arturlangner/Open-OBD2-datalogger/software/obdlogger/Includes/MKE06Z4.h

/*
** ###################################################################
**     Compilers:           ARM Compiler
**                          Freescale C/C++ for Embedded ARM
**                          GNU C Compiler
**                          GNU C Compiler - CodeSourcery Sourcery G++
**                          IAR ANSI C/C++ Compiler for ARM
**
**     Reference manual:    MKE06P80M48SF0RM, Rev. 1, Dec 2013
**     Version:             rev. 1.4, 2014-05-28
**     Build:               b140528
**
**     Abstract:
**         CMSIS Peripheral Access Layer for MKE06Z4
**
**     Copyright (c) 1997 - 2015 Freescale Semiconductor, Inc.
**     All rights reserved.
**
**     Redistribution and use in source and binary forms, with or without modification,
**     are permitted provided that the following conditions are met:
**
**     o Redistributions of source code must retain the above copyright notice, this list
**       of conditions and the following disclaimer.
**
**     o Redistributions in binary form must reproduce the above copyright notice, this
**       list of conditions and the following disclaimer in the documentation and/or
**       other materials provided with the distribution.
**
**     o Neither the name of Freescale Semiconductor, Inc. nor the names of its
**       contributors may be used to endorse or promote products derived from this
**       software without specific prior written permission.
**
**     THIS SOFTWARE IS PROVIDED BY THE COPYRIGHT HOLDERS AND CONTRIBUTORS "AS IS" AND
**     ANY EXPRESS OR IMPLIED WARRANTIES, INCLUDING, BUT NOT LIMITED TO, THE IMPLIED
**     WARRANTIES OF MERCHANTABILITY AND FITNESS FOR A PARTICULAR PURPOSE ARE
**     DISCLAIMED. IN NO EVENT SHALL THE COPYRIGHT HOLDER OR CONTRIBUTORS BE LIABLE FOR
**     ANY DIRECT, INDIRECT, INCIDENTAL, SPECIAL, EXEMPLARY, OR CONSEQUENTIAL DAMAGES
**     (INCLUDING, BUT NOT LIMITED TO, PROCUREMENT OF SUBSTITUTE GOODS OR SERVICES;
**     LOSS OF USE, DATA, OR PROFITS; OR BUSINESS INTERRUPTION) HOWEVER CAUSED AND ON
**     ANY THEORY OF LIABILITY, WHETHER IN CONTRACT, STRICT LIABILITY, OR TORT
**     (INCLUDING NEGLIGENCE OR OTHERWISE) ARISING IN ANY WAY OUT OF THE USE OF THIS
**     SOFTWARE, EVEN IF ADVISED OF THE POSSIBILITY OF SUCH DAMAGE.
**
**     http:                 www.freescale.com
**     mail:                 support@freescale.com
**
**     Revisions:
**     - rev. 1.0 (2013-07-30)
**         Initial version.
**     - rev. 1.1 (2013-10-29)
**         Definition of BITBAND macros updated to support peripherals with 32-bit acces disabled.
**     - rev. 1.2 (2013-10-30)
**         Update according to reference manual rev. 1.
**     - rev. 1.3 (2014-01-10)
**         CAN module: corrected address of TSIDR1 register.
**         CAN module: corrected name of MSCAN_TDLR bit DLC to TDLC.
**         FTM0 module: added access macro for EXTTRIG register.
**         NVIC module: registers access macros improved.
**         SCB module: unused bits removed, mask, shift macros improved.
**         Defines of interrupt vectors aligned to RM.
**     - rev. 1.4 (2014-05-28)
**         The declaration of clock configurations has been moved to separate header file system_MKE02Z2.h
**         Module access macro {module}_BASES replaced by {module}_BASE_PTRS.
**         I2C module: renamed status register S to S1 to match RM naming.
**
** ###################################################################
*/

/*!
 * @file MKE06Z4.h
 * @version 1.4
 * @date 2014-05-28
 * @brief CMSIS Peripheral Access Layer for MKE06Z4
 *
 * CMSIS Peripheral Access Layer for MKE06Z4
 */


/* ----------------------------------------------------------------------------
   -- MCU activation
   ---------------------------------------------------------------------------- */

/* Prevention from multiple including the same memory map */
#if !defined(MKE06Z4_H_)  /* Check if memory map has not been already included */
#define MKE06Z4_H_
#define MCU_MKE06Z4

/* Check if another memory map has not been also included */
#if (defined(MCU_ACTIVE))
  #error MKE06Z4 memory map: There is already included another memory map. Only one memory map can be included.
#endif /* (defined(MCU_ACTIVE)) */
#define MCU_ACTIVE

#include <stdint.h>

/** Memory map major version (memory maps with equal major version number are
 * compatible) */
#define MCU_MEM_MAP_VERSION 0x0100u
/** Memory map minor version */
#define MCU_MEM_MAP_VERSION_MINOR 0x0004u


/* ----------------------------------------------------------------------------
   -- Interrupt vector numbers
   ---------------------------------------------------------------------------- */

/*!
 * @addtogroup Interrupt_vector_numbers Interrupt vector numbers
 * @{
 */

/** Interrupt Number Definitions */
#define NUMBER_OF_INT_VECTORS 48                 /**< Number of interrupts in the Vector table */

typedef enum IRQn {
  /* Core interrupts */
  NonMaskableInt_IRQn          = -14,              /**< Non Maskable Interrupt */
  HardFault_IRQn               = -13,              /**< Cortex-M0 SV Hard Fault Interrupt */
  SVCall_IRQn                  = -5,               /**< Cortex-M0 SV Call Interrupt */
  PendSV_IRQn                  = -2,               /**< Cortex-M0 Pend SV Interrupt */
  SysTick_IRQn                 = -1,               /**< Cortex-M0 System Tick Interrupt */

  /* Device specific interrupts */
  Reserved16_IRQn              = 0,                /**< Reserved interrupt */
  Reserved17_IRQn              = 1,                /**< Reserved interrupt */
  Reserved18_IRQn              = 2,                /**< Reserved interrupt */
  Reserved19_IRQn              = 3,                /**< Reserved interrupt */
  Reserved20_IRQn              = 4,                /**< Reserved interrupt */
  FTMRE_IRQn                   = 5,                /**< Command complete and read collision */
  PMC_IRQn                     = 6,                /**< Low-voltage detect, low-voltage warning */
  IRQ_IRQn                     = 7,                /**< External Interrupt */
  I2C0_IRQn                    = 8,                /**< I2C0 interrupt */
  I2C1_IRQn                    = 9,                /**< I2C1 interrupt */
  SPI0_IRQn                    = 10,               /**< SPI0 single interrupt vector for all sources */
  SPI1_IRQn                    = 11,               /**< SPI1 single interrupt vector for all sources */
  UART0_IRQn                   = 12,               /**< UART0 status and error */
  UART1_IRQn                   = 13,               /**< UART1 status and error */
  UART2_IRQn                   = 14,               /**< UART2 status and error */
  ADC_IRQn                     = 15,               /**< ADC interrupt */
  ACMP0_IRQn                   = 16,               /**< ACMP0 interrupt */
  FTM0_IRQn                    = 17,               /**< FTM0 single interrupt vector for all sources */
  FTM1_IRQn                    = 18,               /**< FTM1 single interrupt vector for all sources */
  FTM2_IRQn                    = 19,               /**< FTM2 single interrupt vector for all sources */
  RTC_IRQn                     = 20,               /**< RTC overflow */
  ACMP1_IRQn                   = 21,               /**< ACMP1 interrupt */
  PIT_CH0_IRQn                 = 22,               /**< PIT CH0 overflow */
  PIT_CH1_IRQn                 = 23,               /**< PIT CH1 overflow */
  KBI0_IRQn                    = 24,               /**< Keyboard interrupt0(32bit) */
  KBI1_IRQn                    = 25,               /**< Keyboard interrupt1(32bit) */
  Reserved42_IRQn              = 26,               /**< Reserved interrupt */
  ICS_IRQn                     = 27,               /**< ICS interrupt */
  WDOG_IRQn                    = 28,               /**< Watchdog timeout */
  PWT_IRQn                     = 29,               /**< PWT interrupt */
  MSCAN_RX_IRQn                = 30,               /**< MSCAN Rx Interrupt */
  MSCAN_TX_IRQn                = 31                /**< MSCAN Tx, Err and Wake-up interrupt */
} IRQn_Type;

/*!
 * @}
 */ /* end of group Interrupt_vector_numbers */


/* ----------------------------------------------------------------------------
   -- Cortex M0 Core Configuration
   ---------------------------------------------------------------------------- */

/*!
 * @addtogroup Cortex_Core_Configuration Cortex M0 Core Configuration
 * @{
 */

#define __CM0PLUS_REV                  0x0000    /**< Core revision r0p0 */
#define __MPU_PRESENT                  0         /**< Defines if an MPU is present or not */
#define __VTOR_PRESENT                 1         /**< Defines if an MPU is present or not */
#define __NVIC_PRIO_BITS               2         /**< Number of priority bits implemented in the NVIC */
#define __Vendor_SysTickConfig         0         /**< Vendor specific implementation of SysTickConfig is defined */

#include "core_cm0plus.h"              /* Core Peripheral Access Layer */
#include "system_MKE06Z4.h"            /* Device specific configuration file */

/*!
 * @}
 */ /* end of group Cortex_Core_Configuration */


/* ----------------------------------------------------------------------------
   -- Device Peripheral Access Layer
   ---------------------------------------------------------------------------- */

/*!
 * @addtogroup Peripheral_access_layer Device Peripheral Access Layer
 * @{
 */


/*
** Start of section using anonymous unions
*/

#if defined(__ARMCC_VERSION)
  #pragma push
  #pragma anon_unions
#elif defined(__CWCC__)
  #pragma push
  #pragma cpp_extensions on
#elif defined(__GNUC__)
  /* anonymous unions are enabled by default */
#elif defined(__IAR_SYSTEMS_ICC__)
  #pragma language=extended
#else
  #error Not supported compiler type
#endif

/* ----------------------------------------------------------------------------
   -- ACMP Peripheral Access Layer
   ---------------------------------------------------------------------------- */

/*!
 * @addtogroup ACMP_Peripheral_Access_Layer ACMP Peripheral Access Layer
 * @{
 */

/** ACMP - Register Layout Typedef */
typedef struct {
  __IO uint8_t CS;                                 /**< ACMP Control and Status Register, offset: 0x0 */
  __IO uint8_t C0;                                 /**< ACMP Control Register 0, offset: 0x1 */
  __IO uint8_t C1;                                 /**< ACMP Control Register 1, offset: 0x2 */
  __IO uint8_t C2;                                 /**< ACMP Control Register 2, offset: 0x3 */
} ACMP_Type, *ACMP_MemMapPtr;

/* ----------------------------------------------------------------------------
   -- ACMP - Register accessor macros
   ---------------------------------------------------------------------------- */

/*!
 * @addtogroup ACMP_Register_Accessor_Macros ACMP - Register accessor macros
 * @{
 */


/* ACMP - Register accessors */
#define ACMP_CS_REG(base)                        ((base)->CS)
#define ACMP_C0_REG(base)                        ((base)->C0)
#define ACMP_C1_REG(base)                        ((base)->C1)
#define ACMP_C2_REG(base)                        ((base)->C2)

/*!
 * @}
 */ /* end of group ACMP_Register_Accessor_Macros */


/* ----------------------------------------------------------------------------
   -- ACMP Register Masks
   ---------------------------------------------------------------------------- */

/*!
 * @addtogroup ACMP_Register_Masks ACMP Register Masks
 * @{
 */

/* CS Bit Fields */
#define ACMP_CS_ACMOD_MASK                       0x3u
#define ACMP_CS_ACMOD_SHIFT                      0
#define ACMP_CS_ACMOD(x)                         (((uint8_t)(((uint8_t)(x))<<ACMP_CS_ACMOD_SHIFT))&ACMP_CS_ACMOD_MASK)
#define ACMP_CS_ACOPE_MASK                       0x4u
#define ACMP_CS_ACOPE_SHIFT                      2
#define ACMP_CS_ACO_MASK                         0x8u
#define ACMP_CS_ACO_SHIFT                        3
#define ACMP_CS_ACIE_MASK                        0x10u
#define ACMP_CS_ACIE_SHIFT                       4
#define ACMP_CS_ACF_MASK                         0x20u
#define ACMP_CS_ACF_SHIFT                        5
#define ACMP_CS_HYST_MASK                        0x40u
#define ACMP_CS_HYST_SHIFT                       6
#define ACMP_CS_ACE_MASK                         0x80u
#define ACMP_CS_ACE_SHIFT                        7
/* C0 Bit Fields */
#define ACMP_C0_ACNSEL_MASK                      0x3u
#define ACMP_C0_ACNSEL_SHIFT                     0
#define ACMP_C0_ACNSEL(x)                        (((uint8_t)(((uint8_t)(x))<<ACMP_C0_ACNSEL_SHIFT))&ACMP_C0_ACNSEL_MASK)
#define ACMP_C0_ACPSEL_MASK                      0x30u
#define ACMP_C0_ACPSEL_SHIFT                     4
#define ACMP_C0_ACPSEL(x)                        (((uint8_t)(((uint8_t)(x))<<ACMP_C0_ACPSEL_SHIFT))&ACMP_C0_ACPSEL_MASK)
/* C1 Bit Fields */
#define ACMP_C1_DACVAL_MASK                      0x3Fu
#define ACMP_C1_DACVAL_SHIFT                     0
#define ACMP_C1_DACVAL(x)                        (((uint8_t)(((uint8_t)(x))<<ACMP_C1_DACVAL_SHIFT))&ACMP_C1_DACVAL_MASK)
#define ACMP_C1_DACREF_MASK                      0x40u
#define ACMP_C1_DACREF_SHIFT                     6
#define ACMP_C1_DACEN_MASK                       0x80u
#define ACMP_C1_DACEN_SHIFT                      7
/* C2 Bit Fields */
#define ACMP_C2_ACIPE_MASK                       0x7u
#define ACMP_C2_ACIPE_SHIFT                      0
#define ACMP_C2_ACIPE(x)                         (((uint8_t)(((uint8_t)(x))<<ACMP_C2_ACIPE_SHIFT))&ACMP_C2_ACIPE_MASK)

/*!
 * @}
 */ /* end of group ACMP_Register_Masks */


/* ACMP - Peripheral instance base addresses */
/** Peripheral ACMP0 base address */
#define ACMP0_BASE                               (0x40073000u)
/** Peripheral ACMP0 base pointer */
#define ACMP0                                    ((ACMP_Type *)ACMP0_BASE)
#define ACMP0_BASE_PTR                           (ACMP0)
/** Peripheral ACMP1 base address */
#define ACMP1_BASE                               (0x40074000u)
/** Peripheral ACMP1 base pointer */
#define ACMP1                                    ((ACMP_Type *)ACMP1_BASE)
#define ACMP1_BASE_PTR                           (ACMP1)
/** Array initializer of ACMP peripheral base addresses */
#define ACMP_BASE_ADDRS                          { ACMP0_BASE, ACMP1_BASE }
/** Array initializer of ACMP peripheral base pointers */
#define ACMP_BASE_PTRS                           { ACMP0, ACMP1 }

/* ----------------------------------------------------------------------------
   -- ACMP - Register accessor macros
   ---------------------------------------------------------------------------- */

/*!
 * @addtogroup ACMP_Register_Accessor_Macros ACMP - Register accessor macros
 * @{
 */


/* ACMP - Register instance definitions */
/* ACMP0 */
#define ACMP0_CS                                 ACMP_CS_REG(ACMP0)
#define ACMP0_C0                                 ACMP_C0_REG(ACMP0)
#define ACMP0_C1                                 ACMP_C1_REG(ACMP0)
#define ACMP0_C2                                 ACMP_C2_REG(ACMP0)
/* ACMP1 */
#define ACMP1_CS                                 ACMP_CS_REG(ACMP1)
#define ACMP1_C0                                 ACMP_C0_REG(ACMP1)
#define ACMP1_C1                                 ACMP_C1_REG(ACMP1)
#define ACMP1_C2                                 ACMP_C2_REG(ACMP1)

/*!
 * @}
 */ /* end of group ACMP_Register_Accessor_Macros */


/*!
 * @}
 */ /* end of group ACMP_Peripheral_Access_Layer */


/* ----------------------------------------------------------------------------
   -- ADC Peripheral Access Layer
   ---------------------------------------------------------------------------- */

/*!
 * @addtogroup ADC_Peripheral_Access_Layer ADC Peripheral Access Layer
 * @{
 */

/** ADC - Register Layout Typedef */
typedef struct {
  __IO uint32_t SC1;                               /**< Status and Control Register 1, offset: 0x0 */
  __IO uint32_t SC2;                               /**< Status and Control Register 2, offset: 0x4 */
  __IO uint32_t SC3;                               /**< Status and Control Register 3, offset: 0x8 */
  __IO uint32_t SC4;                               /**< Status and Control Register 4, offset: 0xC */
  __I  uint32_t R;                                 /**< Conversion Result Register, offset: 0x10 */
  __IO uint32_t CV;                                /**< Compare Value Register, offset: 0x14 */
  __IO uint32_t APCTL1;                            /**< Pin Control 1 Register, offset: 0x18 */
  __IO uint32_t SC5;                               /**< Status and Control Register 5, offset: 0x1C */
} ADC_Type, *ADC_MemMapPtr;

/* ----------------------------------------------------------------------------
   -- ADC - Register accessor macros
   ---------------------------------------------------------------------------- */

/*!
 * @addtogroup ADC_Register_Accessor_Macros ADC - Register accessor macros
 * @{
 */


/* ADC - Register accessors */
#define ADC_SC1_REG(base)                        ((base)->SC1)
#define ADC_SC2_REG(base)                        ((base)->SC2)
#define ADC_SC3_REG(base)                        ((base)->SC3)
#define ADC_SC4_REG(base)                        ((base)->SC4)
#define ADC_R_REG(base)                          ((base)->R)
#define ADC_CV_REG(base)                         ((base)->CV)
#define ADC_APCTL1_REG(base)                     ((base)->APCTL1)
#define ADC_SC5_REG(base)                        ((base)->SC5)

/*!
 * @}
 */ /* end of group ADC_Register_Accessor_Macros */


/* ----------------------------------------------------------------------------
   -- ADC Register Masks
   ---------------------------------------------------------------------------- */

/*!
 * @addtogroup ADC_Register_Masks ADC Register Masks
 * @{
 */

/* SC1 Bit Fields */
#define ADC_SC1_ADCH_MASK                        0x1Fu
#define ADC_SC1_ADCH_SHIFT                       0
#define ADC_SC1_ADCH(x)                          (((uint32_t)(((uint32_t)(x))<<ADC_SC1_ADCH_SHIFT))&ADC_SC1_ADCH_MASK)
#define ADC_SC1_ADCO_MASK                        0x20u
#define ADC_SC1_ADCO_SHIFT                       5
#define ADC_SC1_AIEN_MASK                        0x40u
#define ADC_SC1_AIEN_SHIFT                       6
#define ADC_SC1_COCO_MASK                        0x80u
#define ADC_SC1_COCO_SHIFT                       7
/* SC2 Bit Fields */
#define ADC_SC2_REFSEL_MASK                      0x3u
#define ADC_SC2_REFSEL_SHIFT                     0
#define ADC_SC2_REFSEL(x)                        (((uint32_t)(((uint32_t)(x))<<ADC_SC2_REFSEL_SHIFT))&ADC_SC2_REFSEL_MASK)
#define ADC_SC2_FFULL_MASK                       0x4u
#define ADC_SC2_FFULL_SHIFT                      2
#define ADC_SC2_FEMPTY_MASK                      0x8u
#define ADC_SC2_FEMPTY_SHIFT                     3
#define ADC_SC2_ACFGT_MASK                       0x10u
#define ADC_SC2_ACFGT_SHIFT                      4
#define ADC_SC2_ACFE_MASK                        0x20u
#define ADC_SC2_ACFE_SHIFT                       5
#define ADC_SC2_ADTRG_MASK                       0x40u
#define ADC_SC2_ADTRG_SHIFT                      6
#define ADC_SC2_ADACT_MASK                       0x80u
#define ADC_SC2_ADACT_SHIFT                      7
/* SC3 Bit Fields */
#define ADC_SC3_ADICLK_MASK                      0x3u
#define ADC_SC3_ADICLK_SHIFT                     0
#define ADC_SC3_ADICLK(x)                        (((uint32_t)(((uint32_t)(x))<<ADC_SC3_ADICLK_SHIFT))&ADC_SC3_ADICLK_MASK)
#define ADC_SC3_MODE_MASK                        0xCu
#define ADC_SC3_MODE_SHIFT                       2
#define ADC_SC3_MODE(x)                          (((uint32_t)(((uint32_t)(x))<<ADC_SC3_MODE_SHIFT))&ADC_SC3_MODE_MASK)
#define ADC_SC3_ADLSMP_MASK                      0x10u
#define ADC_SC3_ADLSMP_SHIFT                     4
#define ADC_SC3_ADIV_MASK                        0x60u
#define ADC_SC3_ADIV_SHIFT                       5
#define ADC_SC3_ADIV(x)                          (((uint32_t)(((uint32_t)(x))<<ADC_SC3_ADIV_SHIFT))&ADC_SC3_ADIV_MASK)
#define ADC_SC3_ADLPC_MASK                       0x80u
#define ADC_SC3_ADLPC_SHIFT                      7
/* SC4 Bit Fields */
#define ADC_SC4_AFDEP_MASK                       0x7u
#define ADC_SC4_AFDEP_SHIFT                      0
#define ADC_SC4_AFDEP(x)                         (((uint32_t)(((uint32_t)(x))<<ADC_SC4_AFDEP_SHIFT))&ADC_SC4_AFDEP_MASK)
#define ADC_SC4_ACFSEL_MASK                      0x20u
#define ADC_SC4_ACFSEL_SHIFT                     5
#define ADC_SC4_ASCANE_MASK                      0x40u
#define ADC_SC4_ASCANE_SHIFT                     6
#define ADC_SC4_HTRGME_MASK                      0x100u
#define ADC_SC4_HTRGME_SHIFT                     8
/* R Bit Fields */
#define ADC_R_ADR_MASK                           0xFFFu
#define ADC_R_ADR_SHIFT                          0
#define ADC_R_ADR(x)                             (((uint32_t)(((uint32_t)(x))<<ADC_R_ADR_SHIFT))&ADC_R_ADR_MASK)
/* CV Bit Fields */
#define ADC_CV_CV_MASK                           0xFFFu
#define ADC_CV_CV_SHIFT                          0
#define ADC_CV_CV(x)                             (((uint32_t)(((uint32_t)(x))<<ADC_CV_CV_SHIFT))&ADC_CV_CV_MASK)
/* APCTL1 Bit Fields */
#define ADC_APCTL1_ADPC_MASK                     0xFFFFu
#define ADC_APCTL1_ADPC_SHIFT                    0
#define ADC_APCTL1_ADPC(x)                       (((uint32_t)(((uint32_t)(x))<<ADC_APCTL1_ADPC_SHIFT))&ADC_APCTL1_ADPC_MASK)
/* SC5 Bit Fields */
#define ADC_SC5_HTRGMASKSEL_MASK                 0x1u
#define ADC_SC5_HTRGMASKSEL_SHIFT                0
#define ADC_SC5_HTRGMASKE_MASK                   0x2u
#define ADC_SC5_HTRGMASKE_SHIFT                  1

/*!
 * @}
 */ /* end of group ADC_Register_Masks */


/* ADC - Peripheral instance base addresses */
/** Peripheral ADC base address */
#define ADC_BASE                                 (0x4003B000u)
/** Peripheral ADC base pointer */
#define ADC                                      ((ADC_Type *)ADC_BASE)
#define ADC_BASE_PTR                             (ADC)
/** Array initializer of ADC peripheral base addresses */
#define ADC_BASE_ADDRS                           { ADC_BASE }
/** Array initializer of ADC peripheral base pointers */
#define ADC_BASE_PTRS                            { ADC }

/* ----------------------------------------------------------------------------
   -- ADC - Register accessor macros
   ---------------------------------------------------------------------------- */

/*!
 * @addtogroup ADC_Register_Accessor_Macros ADC - Register accessor macros
 * @{
 */


/* ADC - Register instance definitions */
/* ADC */
#define ADC_SC1                                  ADC_SC1_REG(ADC)
#define ADC_SC2                                  ADC_SC2_REG(ADC)
#define ADC_SC3                                  ADC_SC3_REG(ADC)
#define ADC_SC4                                  ADC_SC4_REG(ADC)
#define ADC_R                                    ADC_R_REG(ADC)
#define ADC_CV                                   ADC_CV_REG(ADC)
#define ADC_APCTL1                               ADC_APCTL1_REG(ADC)
#define ADC_SC5                                  ADC_SC5_REG(ADC)

/*!
 * @}
 */ /* end of group ADC_Register_Accessor_Macros */


/*!
 * @}
 */ /* end of group ADC_Peripheral_Access_Layer */


/* ----------------------------------------------------------------------------
   -- CRC Peripheral Access Layer
   ---------------------------------------------------------------------------- */

/*!
 * @addtogroup CRC_Peripheral_Access_Layer CRC Peripheral Access Layer
 * @{
 */

/** CRC - Register Layout Typedef */
typedef struct {
  union {                                          /* offset: 0x0 */
    struct {                                         /* offset: 0x0 */
      __IO uint16_t DATAL;                             /**< CRC_DATAL register., offset: 0x0 */
      __IO uint16_t DATAH;                             /**< CRC_DATAH register., offset: 0x2 */
    } ACCESS16BIT;
    __IO uint32_t DATA;                              /**< CRC Data register, offset: 0x0 */
    struct {                                         /* offset: 0x0 */
      __IO uint8_t DATALL;                             /**< CRC_DATALL register., offset: 0x0 */
      __IO uint8_t DATALU;                             /**< CRC_DATALU register., offset: 0x1 */
      __IO uint8_t DATAHL;                             /**< CRC_DATAHL register., offset: 0x2 */
      __IO uint8_t DATAHU;                             /**< CRC_DATAHU register., offset: 0x3 */
    } ACCESS8BIT;
  };
  union {                                          /* offset: 0x4 */
    struct {                                         /* offset: 0x4 */
      __IO uint16_t GPOLYL;                            /**< CRC_GPOLYL register., offset: 0x4 */
      __IO uint16_t GPOLYH;                            /**< CRC_GPOLYH register., offset: 0x6 */
    } GPOLY_ACCESS16BIT;
    __IO uint32_t GPOLY;                             /**< CRC Polynomial register, offset: 0x4 */
    struct {                                         /* offset: 0x4 */
      __IO uint8_t GPOLYLL;                            /**< CRC_GPOLYLL register., offset: 0x4 */
      __IO uint8_t GPOLYLU;                            /**< CRC_GPOLYLU register., offset: 0x5 */
      __IO uint8_t GPOLYHL;                            /**< CRC_GPOLYHL register., offset: 0x6 */
      __IO uint8_t GPOLYHU;                            /**< CRC_GPOLYHU register., offset: 0x7 */
    } GPOLY_ACCESS8BIT;
  };
  union {                                          /* offset: 0x8 */
    __IO uint32_t CTRL;                              /**< CRC Control register, offset: 0x8 */
    struct {                                         /* offset: 0x8 */
           uint8_t RESERVED_0[3];
      __IO uint8_t CTRLHU;                             /**< CRC_CTRLHU register., offset: 0xB */
    } CTRL_ACCESS8BIT;
  };
} CRC_Type, *CRC_MemMapPtr;

/* ----------------------------------------------------------------------------
   -- CRC - Register accessor macros
   ---------------------------------------------------------------------------- */

/*!
 * @addtogroup CRC_Register_Accessor_Macros CRC - Register accessor macros
 * @{
 */


/* CRC - Register accessors */
#define CRC_DATAL_REG(base)                      ((base)->ACCESS16BIT.DATAL)
#define CRC_DATAH_REG(base)                      ((base)->ACCESS16BIT.DATAH)
#define CRC_DATA_REG(base)                       ((base)->DATA)
#define CRC_DATALL_REG(base)                     ((base)->ACCESS8BIT.DATALL)
#define CRC_DATALU_REG(base)                     ((base)->ACCESS8BIT.DATALU)
#define CRC_DATAHL_REG(base)                     ((base)->ACCESS8BIT.DATAHL)
#define CRC_DATAHU_REG(base)                     ((base)->ACCESS8BIT.DATAHU)
#define CRC_GPOLYL_REG(base)                     ((base)->GPOLY_ACCESS16BIT.GPOLYL)
#define CRC_GPOLYH_REG(base)                     ((base)->GPOLY_ACCESS16BIT.GPOLYH)
#define CRC_GPOLY_REG(base)                      ((base)->GPOLY)
#define CRC_GPOLYLL_REG(base)                    ((base)->GPOLY_ACCESS8BIT.GPOLYLL)
#define CRC_GPOLYLU_REG(base)                    ((base)->GPOLY_ACCESS8BIT.GPOLYLU)
#define CRC_GPOLYHL_REG(base)                    ((base)->GPOLY_ACCESS8BIT.GPOLYHL)
#define CRC_GPOLYHU_REG(base)                    ((base)->GPOLY_ACCESS8BIT.GPOLYHU)
#define CRC_CTRL_REG(base)                       ((base)->CTRL)
#define CRC_CTRLHU_REG(base)                     ((base)->CTRL_ACCESS8BIT.CTRLHU)

/*!
 * @}
 */ /* end of group CRC_Register_Accessor_Macros */


/* ----------------------------------------------------------------------------
   -- CRC Register Masks
   ---------------------------------------------------------------------------- */

/*!
 * @addtogroup CRC_Register_Masks CRC Register Masks
 * @{
 */

/* DATAL Bit Fields */
#define CRC_DATAL_DATAL_MASK                     0xFFFFu
#define CRC_DATAL_DATAL_SHIFT                    0
#define CRC_DATAL_DATAL(x)                       (((uint16_t)(((uint16_t)(x))<<CRC_DATAL_DATAL_SHIFT))&CRC_DATAL_DATAL_MASK)
/* DATAH Bit Fields */
#define CRC_DATAH_DATAH_MASK                     0xFFFFu
#define CRC_DATAH_DATAH_SHIFT                    0
#define CRC_DATAH_DATAH(x)                       (((uint16_t)(((uint16_t)(x))<<CRC_DATAH_DATAH_SHIFT))&CRC_DATAH_DATAH_MASK)
/* DATA Bit Fields */
#define CRC_DATA_LL_MASK                         0xFFu
#define CRC_DATA_LL_SHIFT                        0
#define CRC_DATA_LL(x)                           (((uint32_t)(((uint32_t)(x))<<CRC_DATA_LL_SHIFT))&CRC_DATA_LL_MASK)
#define CRC_DATA_LU_MASK                         0xFF00u
#define CRC_DATA_LU_SHIFT                        8
#define CRC_DATA_LU(x)                           (((uint32_t)(((uint32_t)(x))<<CRC_DATA_LU_SHIFT))&CRC_DATA_LU_MASK)
#define CRC_DATA_HL_MASK                         0xFF0000u
#define CRC_DATA_HL_SHIFT                        16
#define CRC_DATA_HL(x)                           (((uint32_t)(((uint32_t)(x))<<CRC_DATA_HL_SHIFT))&CRC_DATA_HL_MASK)
#define CRC_DATA_HU_MASK                         0xFF000000u
#define CRC_DATA_HU_SHIFT                        24
#define CRC_DATA_HU(x)                           (((uint32_t)(((uint32_t)(x))<<CRC_DATA_HU_SHIFT))&CRC_DATA_HU_MASK)
/* DATALL Bit Fields */
#define CRC_DATALL_DATALL_MASK                   0xFFu
#define CRC_DATALL_DATALL_SHIFT                  0
#define CRC_DATALL_DATALL(x)                     (((uint8_t)(((uint8_t)(x))<<CRC_DATALL_DATALL_SHIFT))&CRC_DATALL_DATALL_MASK)
/* DATALU Bit Fields */
#define CRC_DATALU_DATALU_MASK                   0xFFu
#define CRC_DATALU_DATALU_SHIFT                  0
#define CRC_DATALU_DATALU(x)                     (((uint8_t)(((uint8_t)(x))<<CRC_DATALU_DATALU_SHIFT))&CRC_DATALU_DATALU_MASK)
/* DATAHL Bit Fields */
#define CRC_DATAHL_DATAHL_MASK                   0xFFu
#define CRC_DATAHL_DATAHL_SHIFT                  0
#define CRC_DATAHL_DATAHL(x)                     (((uint8_t)(((uint8_t)(x))<<CRC_DATAHL_DATAHL_SHIFT))&CRC_DATAHL_DATAHL_MASK)
/* DATAHU Bit Fields */
#define CRC_DATAHU_DATAHU_MASK                   0xFFu
#define CRC_DATAHU_DATAHU_SHIFT                  0
#define CRC_DATAHU_DATAHU(x)                     (((uint8_t)(((uint8_t)(x))<<CRC_DATAHU_DATAHU_SHIFT))&CRC_DATAHU_DATAHU_MASK)
/* GPOLYL Bit Fields */
#define CRC_GPOLYL_GPOLYL_MASK                   0xFFFFu
#define CRC_GPOLYL_GPOLYL_SHIFT                  0
#define CRC_GPOLYL_GPOLYL(x)                     (((uint16_t)(((uint16_t)(x))<<CRC_GPOLYL_GPOLYL_SHIFT))&CRC_GPOLYL_GPOLYL_MASK)
/* GPOLYH Bit Fields */
#define CRC_GPOLYH_GPOLYH_MASK                   0xFFFFu
#define CRC_GPOLYH_GPOLYH_SHIFT                  0
#define CRC_GPOLYH_GPOLYH(x)                     (((uint16_t)(((uint16_t)(x))<<CRC_GPOLYH_GPOLYH_SHIFT))&CRC_GPOLYH_GPOLYH_MASK)
/* GPOLY Bit Fields */
#define CRC_GPOLY_LOW_MASK                       0xFFFFu
#define CRC_GPOLY_LOW_SHIFT                      0
#define CRC_GPOLY_LOW(x)                         (((uint32_t)(((uint32_t)(x))<<CRC_GPOLY_LOW_SHIFT))&CRC_GPOLY_LOW_MASK)
#define CRC_GPOLY_HIGH_MASK                      0xFFFF0000u
#define CRC_GPOLY_HIGH_SHIFT                     16
#define CRC_GPOLY_HIGH(x)                        (((uint32_t)(((uint32_t)(x))<<CRC_GPOLY_HIGH_SHIFT))&CRC_GPOLY_HIGH_MASK)
/* GPOLYLL Bit Fields */
#define CRC_GPOLYLL_GPOLYLL_MASK                 0xFFu
#define CRC_GPOLYLL_GPOLYLL_SHIFT                0
#define CRC_GPOLYLL_GPOLYLL(x)                   (((uint8_t)(((uint8_t)(x))<<CRC_GPOLYLL_GPOLYLL_SHIFT))&CRC_GPOLYLL_GPOLYLL_MASK)
/* GPOLYLU Bit Fields */
#define CRC_GPOLYLU_GPOLYLU_MASK                 0xFFu
#define CRC_GPOLYLU_GPOLYLU_SHIFT                0
#define CRC_GPOLYLU_GPOLYLU(x)                   (((uint8_t)(((uint8_t)(x))<<CRC_GPOLYLU_GPOLYLU_SHIFT))&CRC_GPOLYLU_GPOLYLU_MASK)
/* GPOLYHL Bit Fields */
#define CRC_GPOLYHL_GPOLYHL_MASK                 0xFFu
#define CRC_GPOLYHL_GPOLYHL_SHIFT                0
#define CRC_GPOLYHL_GPOLYHL(x)                   (((uint8_t)(((uint8_t)(x))<<CRC_GPOLYHL_GPOLYHL_SHIFT))&CRC_GPOLYHL_GPOLYHL_MASK)
/* GPOLYHU Bit Fields */
#define CRC_GPOLYHU_GPOLYHU_MASK                 0xFFu
#define CRC_GPOLYHU_GPOLYHU_SHIFT                0
#define CRC_GPOLYHU_GPOLYHU(x)                   (((uint8_t)(((uint8_t)(x))<<CRC_GPOLYHU_GPOLYHU_SHIFT))&CRC_GPOLYHU_GPOLYHU_MASK)
/* CTRL Bit Fields */
#define CRC_CTRL_TCRC_MASK                       0x1000000u
#define CRC_CTRL_TCRC_SHIFT                      24
#define CRC_CTRL_WAS_MASK                        0x2000000u
#define CRC_CTRL_WAS_SHIFT                       25
#define CRC_CTRL_FXOR_MASK                       0x4000000u
#define CRC_CTRL_FXOR_SHIFT                      26
#define CRC_CTRL_TOTR_MASK                       0x30000000u
#define CRC_CTRL_TOTR_SHIFT                      28
#define CRC_CTRL_TOTR(x)                         (((uint32_t)(((uint32_t)(x))<<CRC_CTRL_TOTR_SHIFT))&CRC_CTRL_TOTR_MASK)
#define CRC_CTRL_TOT_MASK                        0xC0000000u
#define CRC_CTRL_TOT_SHIFT                       30
#define CRC_CTRL_TOT(x)                          (((uint32_t)(((uint32_t)(x))<<CRC_CTRL_TOT_SHIFT))&CRC_CTRL_TOT_MASK)
/* CTRLHU Bit Fields */
#define CRC_CTRLHU_TCRC_MASK                     0x1u
#define CRC_CTRLHU_TCRC_SHIFT                    0
#define CRC_CTRLHU_WAS_MASK                      0x2u
#define CRC_CTRLHU_WAS_SHIFT                     1
#define CRC_CTRLHU_FXOR_MASK                     0x4u
#define CRC_CTRLHU_FXOR_SHIFT                    2
#define CRC_CTRLHU_TOTR_MASK                     0x30u
#define CRC_CTRLHU_TOTR_SHIFT                    4
#define CRC_CTRLHU_TOTR(x)                       (((uint8_t)(((uint8_t)(x))<<CRC_CTRLHU_TOTR_SHIFT))&CRC_CTRLHU_TOTR_MASK)
#define CRC_CTRLHU_TOT_MASK                      0xC0u
#define CRC_CTRLHU_TOT_SHIFT                     6
#define CRC_CTRLHU_TOT(x)                        (((uint8_t)(((uint8_t)(x))<<CRC_CTRLHU_TOT_SHIFT))&CRC_CTRLHU_TOT_MASK)

/*!
 * @}
 */ /* end of group CRC_Register_Masks */


/* CRC - Peripheral instance base addresses */
/** Peripheral CRC base address */
#define CRC_BASE                                 (0x40032000u)
/** Peripheral CRC base pointer */
#define CRC0                                     ((CRC_Type *)CRC_BASE)
#define CRC_BASE_PTR                             (CRC0)
/** Array initializer of CRC peripheral base addresses */
#define CRC_BASE_ADDRS                           { CRC_BASE }
/** Array initializer of CRC peripheral base pointers */
#define CRC_BASE_PTRS                            { CRC0 }

/* ----------------------------------------------------------------------------
   -- CRC - Register accessor macros
   ---------------------------------------------------------------------------- */

/*!
 * @addtogroup CRC_Register_Accessor_Macros CRC - Register accessor macros
 * @{
 */


/* CRC - Register instance definitions */
/* CRC */
#define CRC_DATA                                 CRC_DATA_REG(CRC0)
#define CRC_DATAL                                CRC_DATAL_REG(CRC0)
#define CRC_DATALL                               CRC_DATALL_REG(CRC0)
#define CRC_DATALU                               CRC_DATALU_REG(CRC0)
#define CRC_DATAH                                CRC_DATAH_REG(CRC0)
#define CRC_DATAHL                               CRC_DATAHL_REG(CRC0)
#define CRC_DATAHU                               CRC_DATAHU_REG(CRC0)
#define CRC_GPOLY                                CRC_GPOLY_REG(CRC0)
#define CRC_GPOLYL                               CRC_GPOLYL_REG(CRC0)
#define CRC_GPOLYLL                              CRC_GPOLYLL_REG(CRC0)
#define CRC_GPOLYLU                              CRC_GPOLYLU_REG(CRC0)
#define CRC_GPOLYH                               CRC_GPOLYH_REG(CRC0)
#define CRC_GPOLYHL                              CRC_GPOLYHL_REG(CRC0)
#define CRC_GPOLYHU                              CRC_GPOLYHU_REG(CRC0)
#define CRC_CTRL                                 CRC_CTRL_REG(CRC0)
#define CRC_CTRLHU                               CRC_CTRLHU_REG(CRC0)

/*!
 * @}
 */ /* end of group CRC_Register_Accessor_Macros */


/*!
 * @}
 */ /* end of group CRC_Peripheral_Access_Layer */


/* ----------------------------------------------------------------------------
   -- FGPIO Peripheral Access Layer
   ---------------------------------------------------------------------------- */

/*!
 * @addtogroup FGPIO_Peripheral_Access_Layer FGPIO Peripheral Access Layer
 * @{
 */

/** FGPIO - Register Layout Typedef */
typedef struct {
  __IO uint32_t PDOR;                              /**< Port Data Output Register, offset: 0x0 */
  __O  uint32_t PSOR;                              /**< Port Set Output Register, offset: 0x4 */
  __O  uint32_t PCOR;                              /**< Port Clear Output Register, offset: 0x8 */
  __O  uint32_t PTOR;                              /**< Port Toggle Output Register, offset: 0xC */
  __I  uint32_t PDIR;                              /**< Port Data Input Register, offset: 0x10 */
  __IO uint32_t PDDR;                              /**< Port Data Direction Register, offset: 0x14 */
  __IO uint32_t PIDR;                              /**< Port Input Disable Register, offset: 0x18 */
} FGPIO_Type, *FGPIO_MemMapPtr;

/* ----------------------------------------------------------------------------
   -- FGPIO - Register accessor macros
   ---------------------------------------------------------------------------- */

/*!
 * @addtogroup FGPIO_Register_Accessor_Macros FGPIO - Register accessor macros
 * @{
 */


/* FGPIO - Register accessors */
#define FGPIO_PDOR_REG(base)                     ((base)->PDOR)
#define FGPIO_PSOR_REG(base)                     ((base)->PSOR)
#define FGPIO_PCOR_REG(base)                     ((base)->PCOR)
#define FGPIO_PTOR_REG(base)                     ((base)->PTOR)
#define FGPIO_PDIR_REG(base)                     ((base)->PDIR)
#define FGPIO_PDDR_REG(base)                     ((base)->PDDR)
#define FGPIO_PIDR_REG(base)                     ((base)->PIDR)

/*!
 * @}
 */ /* end of group FGPIO_Register_Accessor_Macros */


/* ----------------------------------------------------------------------------
   -- FGPIO Register Masks
   ---------------------------------------------------------------------------- */

/*!
 * @addtogroup FGPIO_Register_Masks FGPIO Register Masks
 * @{
 */

/* PDOR Bit Fields */
#define FGPIO_PDOR_PDO_MASK                      0xFFFFFFFFu
#define FGPIO_PDOR_PDO_SHIFT                     0
#define FGPIO_PDOR_PDO(x)                        (((uint32_t)(((uint32_t)(x))<<FGPIO_PDOR_PDO_SHIFT))&FGPIO_PDOR_PDO_MASK)
/* PSOR Bit Fields */
#define FGPIO_PSOR_PTSO_MASK                     0xFFFFFFFFu
#define FGPIO_PSOR_PTSO_SHIFT                    0
#define FGPIO_PSOR_PTSO(x)                       (((uint32_t)(((uint32_t)(x))<<FGPIO_PSOR_PTSO_SHIFT))&FGPIO_PSOR_PTSO_MASK)
/* PCOR Bit Fields */
#define FGPIO_PCOR_PTCO_MASK                     0xFFFFFFFFu
#define FGPIO_PCOR_PTCO_SHIFT                    0
#define FGPIO_PCOR_PTCO(x)                       (((uint32_t)(((uint32_t)(x))<<FGPIO_PCOR_PTCO_SHIFT))&FGPIO_PCOR_PTCO_MASK)
/* PTOR Bit Fields */
#define FGPIO_PTOR_PTTO_MASK                     0xFFFFFFFFu
#define FGPIO_PTOR_PTTO_SHIFT                    0
#define FGPIO_PTOR_PTTO(x)                       (((uint32_t)(((uint32_t)(x))<<FGPIO_PTOR_PTTO_SHIFT))&FGPIO_PTOR_PTTO_MASK)
/* PDIR Bit Fields */
#define FGPIO_PDIR_PDI_MASK                      0xFFFFFFFFu
#define FGPIO_PDIR_PDI_SHIFT                     0
#define FGPIO_PDIR_PDI(x)                        (((uint32_t)(((uint32_t)(x))<<FGPIO_PDIR_PDI_SHIFT))&FGPIO_PDIR_PDI_MASK)
/* PDDR Bit Fields */
#define FGPIO_PDDR_PDD_MASK                      0xFFFFFFFFu
#define FGPIO_PDDR_PDD_SHIFT                     0
#define FGPIO_PDDR_PDD(x)                        (((uint32_t)(((uint32_t)(x))<<FGPIO_PDDR_PDD_SHIFT))&FGPIO_PDDR_PDD_MASK)
/* PIDR Bit Fields */
#define FGPIO_PIDR_PID_MASK                      0xFFFFFFFFu
#define FGPIO_PIDR_PID_SHIFT                     0
#define FGPIO_PIDR_PID(x)                        (((uint32_t)(((uint32_t)(x))<<FGPIO_PIDR_PID_SHIFT))&FGPIO_PIDR_PID_MASK)

/*!
 * @}
 */ /* end of group FGPIO_Register_Masks */


/* FGPIO - Peripheral instance base addresses */
/** Peripheral FGPIOA base address */
#define FGPIOA_BASE                              (0xF8000000u)
/** Peripheral FGPIOA base pointer */
#define FGPIOA                                   ((FGPIO_Type *)FGPIOA_BASE)
#define FGPIOA_BASE_PTR                          (FGPIOA)
/** Peripheral FGPIOB base address */
#define FGPIOB_BASE                              (0xF8000040u)
/** Peripheral FGPIOB base pointer */
#define FGPIOB                                   ((FGPIO_Type *)FGPIOB_BASE)
#define FGPIOB_BASE_PTR                          (FGPIOB)
/** Peripheral FGPIOC base address */
#define FGPIOC_BASE                              (0xF8000080u)
/** Peripheral FGPIOC base pointer */
#define FGPIOC                                   ((FGPIO_Type *)FGPIOC_BASE)
#define FGPIOC_BASE_PTR                          (FGPIOC)
/** Array initializer of FGPIO peripheral base addresses */
#define FGPIO_BASE_ADDRS                         { FGPIOA_BASE, FGPIOB_BASE, FGPIOC_BASE }
/** Array initializer of FGPIO peripheral base pointers */
#define FGPIO_BASE_PTRS                          { FGPIOA, FGPIOB, FGPIOC }

/* ----------------------------------------------------------------------------
   -- FGPIO - Register accessor macros
   ---------------------------------------------------------------------------- */

/*!
 * @addtogroup FGPIO_Register_Accessor_Macros FGPIO - Register accessor macros
 * @{
 */


/* FGPIO - Register instance definitions */
/* FGPIOA */
#define FGPIOA_PDOR                              FGPIO_PDOR_REG(FGPIOA)
#define FGPIOA_PSOR                              FGPIO_PSOR_REG(FGPIOA)
#define FGPIOA_PCOR                              FGPIO_PCOR_REG(FGPIOA)
#define FGPIOA_PTOR                              FGPIO_PTOR_REG(FGPIOA)
#define FGPIOA_PDIR                              FGPIO_PDIR_REG(FGPIOA)
#define FGPIOA_PDDR                              FGPIO_PDDR_REG(FGPIOA)
#define FGPIOA_PIDR                              FGPIO_PIDR_REG(FGPIOA)
/* FGPIOB */
#define FGPIOB_PDOR                              FGPIO_PDOR_REG(FGPIOB)
#define FGPIOB_PSOR                              FGPIO_PSOR_REG(FGPIOB)
#define FGPIOB_PCOR                              FGPIO_PCOR_REG(FGPIOB)
#define FGPIOB_PTOR                              FGPIO_PTOR_REG(FGPIOB)
#define FGPIOB_PDIR                              FGPIO_PDIR_REG(FGPIOB)
#define FGPIOB_PDDR                              FGPIO_PDDR_REG(FGPIOB)
#define FGPIOB_PIDR                              FGPIO_PIDR_REG(FGPIOB)
/* FGPIOC */
#define FGPIOC_PDOR                              FGPIO_PDOR_REG(FGPIOC)
#define FGPIOC_PSOR                              FGPIO_PSOR_REG(FGPIOC)
#define FGPIOC_PCOR                              FGPIO_PCOR_REG(FGPIOC)
#define FGPIOC_PTOR                              FGPIO_PTOR_REG(FGPIOC)
#define FGPIOC_PDIR                              FGPIO_PDIR_REG(FGPIOC)
#define FGPIOC_PDDR                              FGPIO_PDDR_REG(FGPIOC)
#define FGPIOC_PIDR                              FGPIO_PIDR_REG(FGPIOC)

/*!
 * @}
 */ /* end of group FGPIO_Register_Accessor_Macros */


/*!
 * @}
 */ /* end of group FGPIO_Peripheral_Access_Layer */


/* ----------------------------------------------------------------------------
   -- FTM Peripheral Access Layer
   ---------------------------------------------------------------------------- */

/*!
 * @addtogroup FTM_Peripheral_Access_Layer FTM Peripheral Access Layer
 * @{
 */

/** FTM - Register Layout Typedef */
typedef struct {
  __IO uint32_t SC;                                /**< Status And Control, offset: 0x0 */
  __IO uint32_t CNT;                               /**< Counter, offset: 0x4 */
  __IO uint32_t MOD;                               /**< Modulo, offset: 0x8 */
  struct {                                         /* offset: 0xC, array step: 0x8 */
    __IO uint32_t CnSC;                              /**< Channel (n) Status And Control, array offset: 0xC, array step: 0x8 */
    __IO uint32_t CnV;                               /**< Channel (n) Value, array offset: 0x10, array step: 0x8 */
  } CONTROLS[6];
       uint8_t RESERVED_0[16];
  __IO uint32_t CNTIN;                             /**< Counter Initial Value, offset: 0x4C */
  __IO uint32_t STATUS;                            /**< Capture And Compare Status, offset: 0x50 */
  __IO uint32_t MODE;                              /**< Features Mode Selection, offset: 0x54 */
  __IO uint32_t SYNC;                              /**< Synchronization, offset: 0x58 */
  __IO uint32_t OUTINIT;                           /**< Initial State For Channels Output, offset: 0x5C */
  __IO uint32_t OUTMASK;                           /**< Output Mask, offset: 0x60 */
  __IO uint32_t COMBINE;                           /**< Function For Linked Channels, offset: 0x64 */
  __IO uint32_t DEADTIME;                          /**< Deadtime Insertion Control, offset: 0x68 */
  __IO uint32_t EXTTRIG;                           /**< FTM External Trigger, offset: 0x6C */
  __IO uint32_t POL;                               /**< Channels Polarity, offset: 0x70 */
  __IO uint32_t FMS;                               /**< Fault Mode Status, offset: 0x74 */
  __IO uint32_t FILTER;                            /**< Input Capture Filter Control, offset: 0x78 */
  __IO uint32_t FLTCTRL;                           /**< Fault Control, offset: 0x7C */
       uint8_t RESERVED_1[4];
  __IO uint32_t CONF;                              /**< Configuration, offset: 0x84 */
  __IO uint32_t FLTPOL;                            /**< FTM Fault Input Polarity, offset: 0x88 */
  __IO uint32_t SYNCONF;                           /**< Synchronization Configuration, offset: 0x8C */
  __IO uint32_t INVCTRL;                           /**< FTM Inverting Control, offset: 0x90 */
  __IO uint32_t SWOCTRL;                           /**< FTM Software Output Control, offset: 0x94 */
  __IO uint32_t PWMLOAD;                           /**< FTM PWM Load, offset: 0x98 */
} FTM_Type, *FTM_MemMapPtr;

/* ----------------------------------------------------------------------------
   -- FTM - Register accessor macros
   ---------------------------------------------------------------------------- */

/*!
 * @addtogroup FTM_Register_Accessor_Macros FTM - Register accessor macros
 * @{
 */


/* FTM - Register accessors */
#define FTM_SC_REG(base)                         ((base)->SC)
#define FTM_CNT_REG(base)                        ((base)->CNT)
#define FTM_MOD_REG(base)                        ((base)->MOD)
#define FTM_CnSC_REG(base,index)                 ((base)->CONTROLS[index].CnSC)
#define FTM_CnV_REG(base,index)                  ((base)->CONTROLS[index].CnV)
#define FTM_CNTIN_REG(base)                      ((base)->CNTIN)
#define FTM_STATUS_REG(base)                     ((base)->STATUS)
#define FTM_MODE_REG(base)                       ((base)->MODE)
#define FTM_SYNC_REG(base)                       ((base)->SYNC)
#define FTM_OUTINIT_REG(base)                    ((base)->OUTINIT)
#define FTM_OUTMASK_REG(base)                    ((base)->OUTMASK)
#define FTM_COMBINE_REG(base)                    ((base)->COMBINE)
#define FTM_DEADTIME_REG(base)                   ((base)->DEADTIME)
#define FTM_EXTTRIG_REG(base)                    ((base)->EXTTRIG)
#define FTM_POL_REG(base)                        ((base)->POL)
#define FTM_FMS_REG(base)                        ((base)->FMS)
#define FTM_FILTER_REG(base)                     ((base)->FILTER)
#define FTM_FLTCTRL_REG(base)                    ((base)->FLTCTRL)
#define FTM_CONF_REG(base)                       ((base)->CONF)
#define FTM_FLTPOL_REG(base)                     ((base)->FLTPOL)
#define FTM_SYNCONF_REG(base)                    ((base)->SYNCONF)
#define FTM_INVCTRL_REG(base)                    ((base)->INVCTRL)
#define FTM_SWOCTRL_REG(base)                    ((base)->SWOCTRL)
#define FTM_PWMLOAD_REG(base)                    ((base)->PWMLOAD)

/*!
 * @}
 */ /* end of group FTM_Register_Accessor_Macros */


/* ----------------------------------------------------------------------------
   -- FTM Register Masks
   ---------------------------------------------------------------------------- */

/*!
 * @addtogroup FTM_Register_Masks FTM Register Masks
 * @{
 */

/* SC Bit Fields */
#define FTM_SC_PS_MASK                           0x7u
#define FTM_SC_PS_SHIFT                          0
#define FTM_SC_PS(x)                             (((uint32_t)(((uint32_t)(x))<<FTM_SC_PS_SHIFT))&FTM_SC_PS_MASK)
#define FTM_SC_CLKS_MASK                         0x18u
#define FTM_SC_CLKS_SHIFT                        3
#define FTM_SC_CLKS(x)                           (((uint32_t)(((uint32_t)(x))<<FTM_SC_CLKS_SHIFT))&FTM_SC_CLKS_MASK)
#define FTM_SC_CPWMS_MASK                        0x20u
#define FTM_SC_CPWMS_SHIFT                       5
#define FTM_SC_TOIE_MASK                         0x40u
#define FTM_SC_TOIE_SHIFT                        6
#define FTM_SC_TOF_MASK                          0x80u
#define FTM_SC_TOF_SHIFT                         7
/* CNT Bit Fields */
#define FTM_CNT_COUNT_MASK                       0xFFFFu
#define FTM_CNT_COUNT_SHIFT                      0
#define FTM_CNT_COUNT(x)                         (((uint32_t)(((uint32_t)(x))<<FTM_CNT_COUNT_SHIFT))&FTM_CNT_COUNT_MASK)
/* MOD Bit Fields */
#define FTM_MOD_MOD_MASK                         0xFFFFu
#define FTM_MOD_MOD_SHIFT                        0
#define FTM_MOD_MOD(x)                           (((uint32_t)(((uint32_t)(x))<<FTM_MOD_MOD_SHIFT))&FTM_MOD_MOD_MASK)
/* CnSC Bit Fields */
#define FTM_CnSC_ELSA_MASK                       0x4u
#define FTM_CnSC_ELSA_SHIFT                      2
#define FTM_CnSC_ELSB_MASK                       0x8u
#define FTM_CnSC_ELSB_SHIFT                      3
#define FTM_CnSC_MSA_MASK                        0x10u
#define FTM_CnSC_MSA_SHIFT                       4
#define FTM_CnSC_MSB_MASK                        0x20u
#define FTM_CnSC_MSB_SHIFT                       5
#define FTM_CnSC_CHIE_MASK                       0x40u
#define FTM_CnSC_CHIE_SHIFT                      6
#define FTM_CnSC_CHF_MASK                        0x80u
#define FTM_CnSC_CHF_SHIFT                       7
/* CnV Bit Fields */
#define FTM_CnV_VAL_MASK                         0xFFFFu
#define FTM_CnV_VAL_SHIFT                        0
#define FTM_CnV_VAL(x)                           (((uint32_t)(((uint32_t)(x))<<FTM_CnV_VAL_SHIFT))&FTM_CnV_VAL_MASK)
/* CNTIN Bit Fields */
#define FTM_CNTIN_INIT_MASK                      0xFFFFu
#define FTM_CNTIN_INIT_SHIFT                     0
#define FTM_CNTIN_INIT(x)                        (((uint32_t)(((uint32_t)(x))<<FTM_CNTIN_INIT_SHIFT))&FTM_CNTIN_INIT_MASK)
/* STATUS Bit Fields */
#define FTM_STATUS_CH0F_MASK                     0x1u
#define FTM_STATUS_CH0F_SHIFT                    0
#define FTM_STATUS_CH1F_MASK                     0x2u
#define FTM_STATUS_CH1F_SHIFT                    1
#define FTM_STATUS_CH2F_MASK                     0x4u
#define FTM_STATUS_CH2F_SHIFT                    2
#define FTM_STATUS_CH3F_MASK                     0x8u
#define FTM_STATUS_CH3F_SHIFT                    3
#define FTM_STATUS_CH4F_MASK                     0x10u
#define FTM_STATUS_CH4F_SHIFT                    4
#define FTM_STATUS_CH5F_MASK                     0x20u
#define FTM_STATUS_CH5F_SHIFT                    5
#define FTM_STATUS_CH6F_MASK                     0x40u
#define FTM_STATUS_CH6F_SHIFT                    6
#define FTM_STATUS_CH7F_MASK                     0x80u
#define FTM_STATUS_CH7F_SHIFT                    7
/* MODE Bit Fields */
#define FTM_MODE_FTMEN_MASK                      0x1u
#define FTM_MODE_FTMEN_SHIFT                     0
#define FTM_MODE_INIT_MASK                       0x2u
#define FTM_MODE_INIT_SHIFT                      1
#define FTM_MODE_WPDIS_MASK                      0x4u
#define FTM_MODE_WPDIS_SHIFT                     2
#define FTM_MODE_PWMSYNC_MASK                    0x8u
#define FTM_MODE_PWMSYNC_SHIFT                   3
#define FTM_MODE_CAPTEST_MASK                    0x10u
#define FTM_MODE_CAPTEST_SHIFT                   4
#define FTM_MODE_FAULTM_MASK                     0x60u
#define FTM_MODE_FAULTM_SHIFT                    5
#define FTM_MODE_FAULTM(x)                       (((uint32_t)(((uint32_t)(x))<<FTM_MODE_FAULTM_SHIFT))&FTM_MODE_FAULTM_MASK)
#define FTM_MODE_FAULTIE_MASK                    0x80u
#define FTM_MODE_FAULTIE_SHIFT                   7
/* SYNC Bit Fields */
#define FTM_SYNC_CNTMIN_MASK                     0x1u
#define FTM_SYNC_CNTMIN_SHIFT                    0
#define FTM_SYNC_CNTMAX_MASK                     0x2u
#define FTM_SYNC_CNTMAX_SHIFT                    1
#define FTM_SYNC_REINIT_MASK                     0x4u
#define FTM_SYNC_REINIT_SHIFT                    2
#define FTM_SYNC_SYNCHOM_MASK                    0x8u
#define FTM_SYNC_SYNCHOM_SHIFT                   3
#define FTM_SYNC_TRIG0_MASK                      0x10u
#define FTM_SYNC_TRIG0_SHIFT                     4
#define FTM_SYNC_TRIG1_MASK                      0x20u
#define FTM_SYNC_TRIG1_SHIFT                     5
#define FTM_SYNC_TRIG2_MASK                      0x40u
#define FTM_SYNC_TRIG2_SHIFT                     6
#define FTM_SYNC_SWSYNC_MASK                     0x80u
#define FTM_SYNC_SWSYNC_SHIFT                    7
/* OUTINIT Bit Fields */
#define FTM_OUTINIT_CH0OI_MASK                   0x1u
#define FTM_OUTINIT_CH0OI_SHIFT                  0
#define FTM_OUTINIT_CH1OI_MASK                   0x2u
#define FTM_OUTINIT_CH1OI_SHIFT                  1
#define FTM_OUTINIT_CH2OI_MASK                   0x4u
#define FTM_OUTINIT_CH2OI_SHIFT                  2
#define FTM_OUTINIT_CH3OI_MASK                   0x8u
#define FTM_OUTINIT_CH3OI_SHIFT                  3
#define FTM_OUTINIT_CH4OI_MASK                   0x10u
#define FTM_OUTINIT_CH4OI_SHIFT                  4
#define FTM_OUTINIT_CH5OI_MASK                   0x20u
#define FTM_OUTINIT_CH5OI_SHIFT                  5
#define FTM_OUTINIT_CH6OI_MASK                   0x40u
#define FTM_OUTINIT_CH6OI_SHIFT                  6
#define FTM_OUTINIT_CH7OI_MASK                   0x80u
#define FTM_OUTINIT_CH7OI_SHIFT                  7
/* OUTMASK Bit Fields */
#define FTM_OUTMASK_CH0OM_MASK                   0x1u
#define FTM_OUTMASK_CH0OM_SHIFT                  0
#define FTM_OUTMASK_CH1OM_MASK                   0x2u
#define FTM_OUTMASK_CH1OM_SHIFT                  1
#define FTM_OUTMASK_CH2OM_MASK                   0x4u
#define FTM_OUTMASK_CH2OM_SHIFT                  2
#define FTM_OUTMASK_CH3OM_MASK                   0x8u
#define FTM_OUTMASK_CH3OM_SHIFT                  3
#define FTM_OUTMASK_CH4OM_MASK                   0x10u
#define FTM_OUTMASK_CH4OM_SHIFT                  4
#define FTM_OUTMASK_CH5OM_MASK                   0x20u
#define FTM_OUTMASK_CH5OM_SHIFT                  5
#define FTM_OUTMASK_CH6OM_MASK                   0x40u
#define FTM_OUTMASK_CH6OM_SHIFT                  6
#define FTM_OUTMASK_CH7OM_MASK                   0x80u
#define FTM_OUTMASK_CH7OM_SHIFT                  7
/* COMBINE Bit Fields */
#define FTM_COMBINE_COMBINE0_MASK                0x1u
#define FTM_COMBINE_COMBINE0_SHIFT               0
#define FTM_COMBINE_COMP0_MASK                   0x2u
#define FTM_COMBINE_COMP0_SHIFT                  1
#define FTM_COMBINE_DECAPEN0_MASK                0x4u
#define FTM_COMBINE_DECAPEN0_SHIFT               2
#define FTM_COMBINE_DECAP0_MASK                  0x8u
#define FTM_COMBINE_DECAP0_SHIFT                 3
#define FTM_COMBINE_DTEN0_MASK                   0x10u
#define FTM_COMBINE_DTEN0_SHIFT                  4
#define FTM_COMBINE_SYNCEN0_MASK                 0x20u
#define FTM_COMBINE_SYNCEN0_SHIFT                5
#define FTM_COMBINE_FAULTEN0_MASK                0x40u
#define FTM_COMBINE_FAULTEN0_SHIFT               6
#define FTM_COMBINE_COMBINE1_MASK                0x100u
#define FTM_COMBINE_COMBINE1_SHIFT               8
#define FTM_COMBINE_COMP1_MASK                   0x200u
#define FTM_COMBINE_COMP1_SHIFT                  9
#define FTM_COMBINE_DECAPEN1_MASK                0x400u
#define FTM_COMBINE_DECAPEN1_SHIFT               10
#define FTM_COMBINE_DECAP1_MASK                  0x800u
#define FTM_COMBINE_DECAP1_SHIFT                 11
#define FTM_COMBINE_DTEN1_MASK                   0x1000u
#define FTM_COMBINE_DTEN1_SHIFT                  12
#define FTM_COMBINE_SYNCEN1_MASK                 0x2000u
#define FTM_COMBINE_SYNCEN1_SHIFT                13
#define FTM_COMBINE_FAULTEN1_MASK                0x4000u
#define FTM_COMBINE_FAULTEN1_SHIFT               14
#define FTM_COMBINE_COMBINE2_MASK                0x10000u
#define FTM_COMBINE_COMBINE2_SHIFT               16
#define FTM_COMBINE_COMP2_MASK                   0x20000u
#define FTM_COMBINE_COMP2_SHIFT                  17
#define FTM_COMBINE_DECAPEN2_MASK                0x40000u
#define FTM_COMBINE_DECAPEN2_SHIFT               18
#define FTM_COMBINE_DECAP2_MASK                  0x80000u
#define FTM_COMBINE_DECAP2_SHIFT                 19
#define FTM_COMBINE_DTEN2_MASK                   0x100000u
#define FTM_COMBINE_DTEN2_SHIFT                  20
#define FTM_COMBINE_SYNCEN2_MASK                 0x200000u
#define FTM_COMBINE_SYNCEN2_SHIFT                21
#define FTM_COMBINE_FAULTEN2_MASK                0x400000u
#define FTM_COMBINE_FAULTEN2_SHIFT               22
#define FTM_COMBINE_COMBINE3_MASK                0x1000000u
#define FTM_COMBINE_COMBINE3_SHIFT               24
#define FTM_COMBINE_COMP3_MASK                   0x2000000u
#define FTM_COMBINE_COMP3_SHIFT                  25
#define FTM_COMBINE_DECAPEN3_MASK                0x4000000u
#define FTM_COMBINE_DECAPEN3_SHIFT               26
#define FTM_COMBINE_DECAP3_MASK                  0x8000000u
#define FTM_COMBINE_DECAP3_SHIFT                 27
#define FTM_COMBINE_DTEN3_MASK                   0x10000000u
#define FTM_COMBINE_DTEN3_SHIFT                  28
#define FTM_COMBINE_SYNCEN3_MASK                 0x20000000u
#define FTM_COMBINE_SYNCEN3_SHIFT                29
#define FTM_COMBINE_FAULTEN3_MASK                0x40000000u
#define FTM_COMBINE_FAULTEN3_SHIFT               30
/* DEADTIME Bit Fields */
#define FTM_DEADTIME_DTVAL_MASK                  0x3Fu
#define FTM_DEADTIME_DTVAL_SHIFT                 0
#define FTM_DEADTIME_DTVAL(x)                    (((uint32_t)(((uint32_t)(x))<<FTM_DEADTIME_DTVAL_SHIFT))&FTM_DEADTIME_DTVAL_MASK)
#define FTM_DEADTIME_DTPS_MASK                   0xC0u
#define FTM_DEADTIME_DTPS_SHIFT                  6
#define FTM_DEADTIME_DTPS(x)                     (((uint32_t)(((uint32_t)(x))<<FTM_DEADTIME_DTPS_SHIFT))&FTM_DEADTIME_DTPS_MASK)
/* EXTTRIG Bit Fields */
#define FTM_EXTTRIG_CH2TRIG_MASK                 0x1u
#define FTM_EXTTRIG_CH2TRIG_SHIFT                0
#define FTM_EXTTRIG_CH3TRIG_MASK                 0x2u
#define FTM_EXTTRIG_CH3TRIG_SHIFT                1
#define FTM_EXTTRIG_CH4TRIG_MASK                 0x4u
#define FTM_EXTTRIG_CH4TRIG_SHIFT                2
#define FTM_EXTTRIG_CH5TRIG_MASK                 0x8u
#define FTM_EXTTRIG_CH5TRIG_SHIFT                3
#define FTM_EXTTRIG_CH0TRIG_MASK                 0x10u
#define FTM_EXTTRIG_CH0TRIG_SHIFT                4
#define FTM_EXTTRIG_CH1TRIG_MASK                 0x20u
#define FTM_EXTTRIG_CH1TRIG_SHIFT                5
#define FTM_EXTTRIG_INITTRIGEN_MASK              0x40u
#define FTM_EXTTRIG_INITTRIGEN_SHIFT             6
#define FTM_EXTTRIG_TRIGF_MASK                   0x80u
#define FTM_EXTTRIG_TRIGF_SHIFT                  7
/* POL Bit Fields */
#define FTM_POL_POL0_MASK                        0x1u
#define FTM_POL_POL0_SHIFT                       0
#define FTM_POL_POL1_MASK                        0x2u
#define FTM_POL_POL1_SHIFT                       1
#define FTM_POL_POL2_MASK                        0x4u
#define FTM_POL_POL2_SHIFT                       2
#define FTM_POL_POL3_MASK                        0x8u
#define FTM_POL_POL3_SHIFT                       3
#define FTM_POL_POL4_MASK                        0x10u
#define FTM_POL_POL4_SHIFT                       4
#define FTM_POL_POL5_MASK                        0x20u
#define FTM_POL_POL5_SHIFT                       5
#define FTM_POL_POL6_MASK                        0x40u
#define FTM_POL_POL6_SHIFT                       6
#define FTM_POL_POL7_MASK                        0x80u
#define FTM_POL_POL7_SHIFT                       7
/* FMS Bit Fields */
#define FTM_FMS_FAULTF0_MASK                     0x1u
#define FTM_FMS_FAULTF0_SHIFT                    0
#define FTM_FMS_FAULTF1_MASK                     0x2u
#define FTM_FMS_FAULTF1_SHIFT                    1
#define FTM_FMS_FAULTF2_MASK                     0x4u
#define FTM_FMS_FAULTF2_SHIFT                    2
#define FTM_FMS_FAULTF3_MASK                     0x8u
#define FTM_FMS_FAULTF3_SHIFT                    3
#define FTM_FMS_FAULTIN_MASK                     0x20u
#define FTM_FMS_FAULTIN_SHIFT                    5
#define FTM_FMS_WPEN_MASK                        0x40u
#define FTM_FMS_WPEN_SHIFT                       6
#define FTM_FMS_FAULTF_MASK                      0x80u
#define FTM_FMS_FAULTF_SHIFT                     7
/* FILTER Bit Fields */
#define FTM_FILTER_CH0FVAL_MASK                  0xFu
#define FTM_FILTER_CH0FVAL_SHIFT                 0
#define FTM_FILTER_CH0FVAL(x)                    (((uint32_t)(((uint32_t)(x))<<FTM_FILTER_CH0FVAL_SHIFT))&FTM_FILTER_CH0FVAL_MASK)
#define FTM_FILTER_CH1FVAL_MASK                  0xF0u
#define FTM_FILTER_CH1FVAL_SHIFT                 4
#define FTM_FILTER_CH1FVAL(x)                    (((uint32_t)(((uint32_t)(x))<<FTM_FILTER_CH1FVAL_SHIFT))&FTM_FILTER_CH1FVAL_MASK)
#define FTM_FILTER_CH2FVAL_MASK                  0xF00u
#define FTM_FILTER_CH2FVAL_SHIFT                 8
#define FTM_FILTER_CH2FVAL(x)                    (((uint32_t)(((uint32_t)(x))<<FTM_FILTER_CH2FVAL_SHIFT))&FTM_FILTER_CH2FVAL_MASK)
#define FTM_FILTER_CH3FVAL_MASK                  0xF000u
#define FTM_FILTER_CH3FVAL_SHIFT                 12
#define FTM_FILTER_CH3FVAL(x)                    (((uint32_t)(((uint32_t)(x))<<FTM_FILTER_CH3FVAL_SHIFT))&FTM_FILTER_CH3FVAL_MASK)
/* FLTCTRL Bit Fields */
#define FTM_FLTCTRL_FAULT0EN_MASK                0x1u
#define FTM_FLTCTRL_FAULT0EN_SHIFT               0
#define FTM_FLTCTRL_FAULT1EN_MASK                0x2u
#define FTM_FLTCTRL_FAULT1EN_SHIFT               1
#define FTM_FLTCTRL_FAULT2EN_MASK                0x4u
#define FTM_FLTCTRL_FAULT2EN_SHIFT               2
#define FTM_FLTCTRL_FAULT3EN_MASK                0x8u
#define FTM_FLTCTRL_FAULT3EN_SHIFT               3
#define FTM_FLTCTRL_FFLTR0EN_MASK                0x10u
#define FTM_FLTCTRL_FFLTR0EN_SHIFT               4
#define FTM_FLTCTRL_FFLTR1EN_MASK                0x20u
#define FTM_FLTCTRL_FFLTR1EN_SHIFT               5
#define FTM_FLTCTRL_FFLTR2EN_MASK                0x40u
#define FTM_FLTCTRL_FFLTR2EN_SHIFT               6
#define FTM_FLTCTRL_FFLTR3EN_MASK                0x80u
#define FTM_FLTCTRL_FFLTR3EN_SHIFT               7
#define FTM_FLTCTRL_FFVAL_MASK                   0xF00u
#define FTM_FLTCTRL_FFVAL_SHIFT                  8
#define FTM_FLTCTRL_FFVAL(x)                     (((uint32_t)(((uint32_t)(x))<<FTM_FLTCTRL_FFVAL_SHIFT))&FTM_FLTCTRL_FFVAL_MASK)
/* CONF Bit Fields */
#define FTM_CONF_NUMTOF_MASK                     0x1Fu
#define FTM_CONF_NUMTOF_SHIFT                    0
#define FTM_CONF_NUMTOF(x)                       (((uint32_t)(((uint32_t)(x))<<FTM_CONF_NUMTOF_SHIFT))&FTM_CONF_NUMTOF_MASK)
#define FTM_CONF_BDMMODE_MASK                    0xC0u
#define FTM_CONF_BDMMODE_SHIFT                   6
#define FTM_CONF_BDMMODE(x)                      (((uint32_t)(((uint32_t)(x))<<FTM_CONF_BDMMODE_SHIFT))&FTM_CONF_BDMMODE_MASK)
#define FTM_CONF_GTBEEN_MASK                     0x200u
#define FTM_CONF_GTBEEN_SHIFT                    9
#define FTM_CONF_GTBEOUT_MASK                    0x400u
#define FTM_CONF_GTBEOUT_SHIFT                   10
/* FLTPOL Bit Fields */
#define FTM_FLTPOL_FLT0POL_MASK                  0x1u
#define FTM_FLTPOL_FLT0POL_SHIFT                 0
#define FTM_FLTPOL_FLT1POL_MASK                  0x2u
#define FTM_FLTPOL_FLT1POL_SHIFT                 1
#define FTM_FLTPOL_FLT2POL_MASK                  0x4u
#define FTM_FLTPOL_FLT2POL_SHIFT                 2
#define FTM_FLTPOL_FLT3POL_MASK                  0x8u
#define FTM_FLTPOL_FLT3POL_SHIFT                 3
/* SYNCONF Bit Fields */
#define FTM_SYNCONF_HWTRIGMODE_MASK              0x1u
#define FTM_SYNCONF_HWTRIGMODE_SHIFT             0
#define FTM_SYNCONF_CNTINC_MASK                  0x4u
#define FTM_SYNCONF_CNTINC_SHIFT                 2
#define FTM_SYNCONF_INVC_MASK                    0x10u
#define FTM_SYNCONF_INVC_SHIFT                   4
#define FTM_SYNCONF_SWOC_MASK                    0x20u
#define FTM_SYNCONF_SWOC_SHIFT                   5
#define FTM_SYNCONF_SYNCMODE_MASK                0x80u
#define FTM_SYNCONF_SYNCMODE_SHIFT               7
#define FTM_SYNCONF_SWRSTCNT_MASK                0x100u
#define FTM_SYNCONF_SWRSTCNT_SHIFT               8
#define FTM_SYNCONF_SWWRBUF_MASK                 0x200u
#define FTM_SYNCONF_SWWRBUF_SHIFT                9
#define FTM_SYNCONF_SWOM_MASK                    0x400u
#define FTM_SYNCONF_SWOM_SHIFT                   10
#define FTM_SYNCONF_SWINVC_MASK                  0x800u
#define FTM_SYNCONF_SWINVC_SHIFT                 11
#define FTM_SYNCONF_SWSOC_MASK                   0x1000u
#define FTM_SYNCONF_SWSOC_SHIFT                  12
#define FTM_SYNCONF_HWRSTCNT_MASK                0x10000u
#define FTM_SYNCONF_HWRSTCNT_SHIFT               16
#define FTM_SYNCONF_HWWRBUF_MASK                 0x20000u
#define FTM_SYNCONF_HWWRBUF_SHIFT                17
#define FTM_SYNCONF_HWOM_MASK                    0x40000u
#define FTM_SYNCONF_HWOM_SHIFT                   18
#define FTM_SYNCONF_HWINVC_MASK                  0x80000u
#define FTM_SYNCONF_HWINVC_SHIFT                 19
#define FTM_SYNCONF_HWSOC_MASK                   0x100000u
#define FTM_SYNCONF_HWSOC_SHIFT                  20
/* INVCTRL Bit Fields */
#define FTM_INVCTRL_INV0EN_MASK                  0x1u
#define FTM_INVCTRL_INV0EN_SHIFT                 0
#define FTM_INVCTRL_INV1EN_MASK                  0x2u
#define FTM_INVCTRL_INV1EN_SHIFT                 1
#define FTM_INVCTRL_INV2EN_MASK                  0x4u
#define FTM_INVCTRL_INV2EN_SHIFT                 2
#define FTM_INVCTRL_INV3EN_MASK                  0x8u
#define FTM_INVCTRL_INV3EN_SHIFT                 3
/* SWOCTRL Bit Fields */
#define FTM_SWOCTRL_CH0OC_MASK                   0x1u
#define FTM_SWOCTRL_CH0OC_SHIFT                  0
#define FTM_SWOCTRL_CH1OC_MASK                   0x2u
#define FTM_SWOCTRL_CH1OC_SHIFT                  1
#define FTM_SWOCTRL_CH2OC_MASK                   0x4u
#define FTM_SWOCTRL_CH2OC_SHIFT                  2
#define FTM_SWOCTRL_CH3OC_MASK                   0x8u
#define FTM_SWOCTRL_CH3OC_SHIFT                  3
#define FTM_SWOCTRL_CH4OC_MASK                   0x10u
#define FTM_SWOCTRL_CH4OC_SHIFT                  4
#define FTM_SWOCTRL_CH5OC_MASK                   0x20u
#define FTM_SWOCTRL_CH5OC_SHIFT                  5
#define FTM_SWOCTRL_CH6OC_MASK                   0x40u
#define FTM_SWOCTRL_CH6OC_SHIFT                  6
#define FTM_SWOCTRL_CH7OC_MASK                   0x80u
#define FTM_SWOCTRL_CH7OC_SHIFT                  7
#define FTM_SWOCTRL_CH0OCV_MASK                  0x100u
#define FTM_SWOCTRL_CH0OCV_SHIFT                 8
#define FTM_SWOCTRL_CH1OCV_MASK                  0x200u
#define FTM_SWOCTRL_CH1OCV_SHIFT                 9
#define FTM_SWOCTRL_CH2OCV_MASK                  0x400u
#define FTM_SWOCTRL_CH2OCV_SHIFT                 10
#define FTM_SWOCTRL_CH3OCV_MASK                  0x800u
#define FTM_SWOCTRL_CH3OCV_SHIFT                 11
#define FTM_SWOCTRL_CH4OCV_MASK                  0x1000u
#define FTM_SWOCTRL_CH4OCV_SHIFT                 12
#define FTM_SWOCTRL_CH5OCV_MASK                  0x2000u
#define FTM_SWOCTRL_CH5OCV_SHIFT                 13
#define FTM_SWOCTRL_CH6OCV_MASK                  0x4000u
#define FTM_SWOCTRL_CH6OCV_SHIFT                 14
#define FTM_SWOCTRL_CH7OCV_MASK                  0x8000u
#define FTM_SWOCTRL_CH7OCV_SHIFT                 15
/* PWMLOAD Bit Fields */
#define FTM_PWMLOAD_CH0SEL_MASK                  0x1u
#define FTM_PWMLOAD_CH0SEL_SHIFT                 0
#define FTM_PWMLOAD_CH1SEL_MASK                  0x2u
#define FTM_PWMLOAD_CH1SEL_SHIFT                 1
#define FTM_PWMLOAD_CH2SEL_MASK                  0x4u
#define FTM_PWMLOAD_CH2SEL_SHIFT                 2
#define FTM_PWMLOAD_CH3SEL_MASK                  0x8u
#define FTM_PWMLOAD_CH3SEL_SHIFT                 3
#define FTM_PWMLOAD_CH4SEL_MASK                  0x10u
#define FTM_PWMLOAD_CH4SEL_SHIFT                 4
#define FTM_PWMLOAD_CH5SEL_MASK                  0x20u
#define FTM_PWMLOAD_CH5SEL_SHIFT                 5
#define FTM_PWMLOAD_CH6SEL_MASK                  0x40u
#define FTM_PWMLOAD_CH6SEL_SHIFT                 6
#define FTM_PWMLOAD_CH7SEL_MASK                  0x80u
#define FTM_PWMLOAD_CH7SEL_SHIFT                 7
#define FTM_PWMLOAD_LDOK_MASK                    0x200u
#define FTM_PWMLOAD_LDOK_SHIFT                   9

/*!
 * @}
 */ /* end of group FTM_Register_Masks */


/* FTM - Peripheral instance base addresses */
/** Peripheral FTM0 base address */
#define FTM0_BASE                                (0x40038000u)
/** Peripheral FTM0 base pointer */
#define FTM0                                     ((FTM_Type *)FTM0_BASE)
#define FTM0_BASE_PTR                            (FTM0)
/** Peripheral FTM1 base address */
#define FTM1_BASE                                (0x40039000u)
/** Peripheral FTM1 base pointer */
#define FTM1                                     ((FTM_Type *)FTM1_BASE)
#define FTM1_BASE_PTR                            (FTM1)
/** Peripheral FTM2 base address */
#define FTM2_BASE                                (0x4003A000u)
/** Peripheral FTM2 base pointer */
#define FTM2                                     ((FTM_Type *)FTM2_BASE)
#define FTM2_BASE_PTR                            (FTM2)
/** Array initializer of FTM peripheral base addresses */
#define FTM_BASE_ADDRS                           { FTM0_BASE, FTM1_BASE, FTM2_BASE }
/** Array initializer of FTM peripheral base pointers */
#define FTM_BASE_PTRS                            { FTM0, FTM1, FTM2 }

/* ----------------------------------------------------------------------------
   -- FTM - Register accessor macros
   ---------------------------------------------------------------------------- */

/*!
 * @addtogroup FTM_Register_Accessor_Macros FTM - Register accessor macros
 * @{
 */


/* FTM - Register instance definitions */
/* FTM0 */
#define FTM0_SC                                  FTM_SC_REG(FTM0)
#define FTM0_CNT                                 FTM_CNT_REG(FTM0)
#define FTM0_MOD                                 FTM_MOD_REG(FTM0)
#define FTM0_C0SC                                FTM_CnSC_REG(FTM0,0)
#define FTM0_C0V                                 FTM_CnV_REG(FTM0,0)
#define FTM0_C1SC                                FTM_CnSC_REG(FTM0,1)
#define FTM0_C1V                                 FTM_CnV_REG(FTM0,1)
#define FTM0_EXTTRIG                             FTM_EXTTRIG_REG(FTM0)
/* FTM1 */
#define FTM1_SC                                  FTM_SC_REG(FTM1)
#define FTM1_CNT                                 FTM_CNT_REG(FTM1)
#define FTM1_MOD                                 FTM_MOD_REG(FTM1)
#define FTM1_C0SC                                FTM_CnSC_REG(FTM1,0)
#define FTM1_C0V                                 FTM_CnV_REG(FTM1,0)
#define FTM1_C1SC                                FTM_CnSC_REG(FTM1,1)
#define FTM1_C1V                                 FTM_CnV_REG(FTM1,1)
/* FTM2 */
#define FTM2_SC                                  FTM_SC_REG(FTM2)
#define FTM2_CNT                                 FTM_CNT_REG(FTM2)
#define FTM2_MOD                                 FTM_MOD_REG(FTM2)
#define FTM2_C0SC                                FTM_CnSC_REG(FTM2,0)
#define FTM2_C0V                                 FTM_CnV_REG(FTM2,0)
#define FTM2_C1SC                                FTM_CnSC_REG(FTM2,1)
#define FTM2_C1V                                 FTM_CnV_REG(FTM2,1)
#define FTM2_C2SC                                FTM_CnSC_REG(FTM2,2)
#define FTM2_C2V                                 FTM_CnV_REG(FTM2,2)
#define FTM2_C3SC                                FTM_CnSC_REG(FTM2,3)
#define FTM2_C3V                                 FTM_CnV_REG(FTM2,3)
#define FTM2_C4SC                                FTM_CnSC_REG(FTM2,4)
#define FTM2_C4V                                 FTM_CnV_REG(FTM2,4)
#define FTM2_C5SC                                FTM_CnSC_REG(FTM2,5)
#define FTM2_C5V                                 FTM_CnV_REG(FTM2,5)
#define FTM2_CNTIN                               FTM_CNTIN_REG(FTM2)
#define FTM2_STATUS                              FTM_STATUS_REG(FTM2)
#define FTM2_MODE                                FTM_MODE_REG(FTM2)
#define FTM2_SYNC                                FTM_SYNC_REG(FTM2)
#define FTM2_OUTINIT                             FTM_OUTINIT_REG(FTM2)
#define FTM2_OUTMASK                             FTM_OUTMASK_REG(FTM2)
#define FTM2_COMBINE                             FTM_COMBINE_REG(FTM2)
#define FTM2_DEADTIME                            FTM_DEADTIME_REG(FTM2)
#define FTM2_EXTTRIG                             FTM_EXTTRIG_REG(FTM2)
#define FTM2_POL                                 FTM_POL_REG(FTM2)
#define FTM2_FMS                                 FTM_FMS_REG(FTM2)
#define FTM2_FILTER                              FTM_FILTER_REG(FTM2)
#define FTM2_FLTCTRL                             FTM_FLTCTRL_REG(FTM2)
#define FTM2_CONF                                FTM_CONF_REG(FTM2)
#define FTM2_FLTPOL                              FTM_FLTPOL_REG(FTM2)
#define FTM2_SYNCONF                             FTM_SYNCONF_REG(FTM2)
#define FTM2_INVCTRL                             FTM_INVCTRL_REG(FTM2)
#define FTM2_SWOCTRL                             FTM_SWOCTRL_REG(FTM2)
#define FTM2_PWMLOAD                             FTM_PWMLOAD_REG(FTM2)

/* FTM - Register array accessors */
#define FTM0_CnSC(index)                         FTM_CnSC_REG(FTM0,index)
#define FTM1_CnSC(index)                         FTM_CnSC_REG(FTM1,index)
#define FTM2_CnSC(index)                         FTM_CnSC_REG(FTM2,index)
#define FTM0_CnV(index)                          FTM_CnV_REG(FTM0,index)
#define FTM1_CnV(index)                          FTM_CnV_REG(FTM1,index)
#define FTM2_CnV(index)                          FTM_CnV_REG(FTM2,index)

/*!
 * @}
 */ /* end of group FTM_Register_Accessor_Macros */


/*!
 * @}
 */ /* end of group FTM_Peripheral_Access_Layer */


/* ----------------------------------------------------------------------------
   -- FTMRE Peripheral Access Layer
   ---------------------------------------------------------------------------- */

/*!
 * @addtogroup FTMRE_Peripheral_Access_Layer FTMRE Peripheral Access Layer
 * @{
 */

/** FTMRE - Register Layout Typedef */
typedef struct {
       uint8_t RESERVED_0[1];
  __IO uint8_t FCCOBIX;                            /**< Flash CCOB Index Register, offset: 0x1 */
  __I  uint8_t FSEC;                               /**< Flash Security Register, offset: 0x2 */
  __IO uint8_t FCLKDIV;                            /**< Flash Clock Divider Register, offset: 0x3 */
       uint8_t RESERVED_1[1];
  __IO uint8_t FSTAT;                              /**< Flash Status Register, offset: 0x5 */
       uint8_t RESERVED_2[1];
  __IO uint8_t FCNFG;                              /**< Flash Configuration Register, offset: 0x7 */
  __IO uint8_t FCCOBLO;                            /**< Flash Common Command Object Register: Low, offset: 0x8 */
  __IO uint8_t FCCOBHI;                            /**< Flash Common Command Object Register:High, offset: 0x9 */
       uint8_t RESERVED_3[1];
  __IO uint8_t FPROT;                              /**< Flash Protection Register, offset: 0xB */
       uint8_t RESERVED_4[3];
  __I  uint8_t FOPT;                               /**< Flash Option Register, offset: 0xF */
} FTMRE_Type, *FTMRE_MemMapPtr;

/* ----------------------------------------------------------------------------
   -- FTMRE - Register accessor macros
   ---------------------------------------------------------------------------- */

/*!
 * @addtogroup FTMRE_Register_Accessor_Macros FTMRE - Register accessor macros
 * @{
 */


/* FTMRE - Register accessors */
#define FTMRE_FCCOBIX_REG(base)                  ((base)->FCCOBIX)
#define FTMRE_FSEC_REG(base)                     ((base)->FSEC)
#define FTMRE_FCLKDIV_REG(base)                  ((base)->FCLKDIV)
#define FTMRE_FSTAT_REG(base)                    ((base)->FSTAT)
#define FTMRE_FCNFG_REG(base)                    ((base)->FCNFG)
#define FTMRE_FCCOBLO_REG(base)                  ((base)->FCCOBLO)
#define FTMRE_FCCOBHI_REG(base)                  ((base)->FCCOBHI)
#define FTMRE_FPROT_REG(base)                    ((base)->FPROT)
#define FTMRE_FOPT_REG(base)                     ((base)->FOPT)

/*!
 * @}
 */ /* end of group FTMRE_Register_Accessor_Macros */


/* ----------------------------------------------------------------------------
   -- FTMRE Register Masks
   ---------------------------------------------------------------------------- */

/*!
 * @addtogroup FTMRE_Register_Masks FTMRE Register Masks
 * @{
 */

/* FCCOBIX Bit Fields */
#define FTMRE_FCCOBIX_CCOBIX_MASK                0x7u
#define FTMRE_FCCOBIX_CCOBIX_SHIFT               0
#define FTMRE_FCCOBIX_CCOBIX(x)                  (((uint8_t)(((uint8_t)(x))<<FTMRE_FCCOBIX_CCOBIX_SHIFT))&FTMRE_FCCOBIX_CCOBIX_MASK)
/* FSEC Bit Fields */
#define FTMRE_FSEC_SEC_MASK                      0x3u
#define FTMRE_FSEC_SEC_SHIFT                     0
#define FTMRE_FSEC_SEC(x)                        (((uint8_t)(((uint8_t)(x))<<FTMRE_FSEC_SEC_SHIFT))&FTMRE_FSEC_SEC_MASK)
#define FTMRE_FSEC_KEYEN_MASK                    0xC0u
#define FTMRE_FSEC_KEYEN_SHIFT                   6
#define FTMRE_FSEC_KEYEN(x)                      (((uint8_t)(((uint8_t)(x))<<FTMRE_FSEC_KEYEN_SHIFT))&FTMRE_FSEC_KEYEN_MASK)
/* FCLKDIV Bit Fields */
#define FTMRE_FCLKDIV_FDIV_MASK                  0x3Fu
#define FTMRE_FCLKDIV_FDIV_SHIFT                 0
#define FTMRE_FCLKDIV_FDIV(x)                    (((uint8_t)(((uint8_t)(x))<<FTMRE_FCLKDIV_FDIV_SHIFT))&FTMRE_FCLKDIV_FDIV_MASK)
#define FTMRE_FCLKDIV_FDIVLCK_MASK               0x40u
#define FTMRE_FCLKDIV_FDIVLCK_SHIFT              6
#define FTMRE_FCLKDIV_FDIVLD_MASK                0x80u
#define FTMRE_FCLKDIV_FDIVLD_SHIFT               7
/* FSTAT Bit Fields */
#define FTMRE_FSTAT_MGSTAT_MASK                  0x3u
#define FTMRE_FSTAT_MGSTAT_SHIFT                 0
#define FTMRE_FSTAT_MGSTAT(x)                    (((uint8_t)(((uint8_t)(x))<<FTMRE_FSTAT_MGSTAT_SHIFT))&FTMRE_FSTAT_MGSTAT_MASK)
#define FTMRE_FSTAT_MGBUSY_MASK                  0x8u
#define FTMRE_FSTAT_MGBUSY_SHIFT                 3
#define FTMRE_FSTAT_FPVIOL_MASK                  0x10u
#define FTMRE_FSTAT_FPVIOL_SHIFT                 4
#define FTMRE_FSTAT_ACCERR_MASK                  0x20u
#define FTMRE_FSTAT_ACCERR_SHIFT                 5
#define FTMRE_FSTAT_CCIF_MASK                    0x80u
#define FTMRE_FSTAT_CCIF_SHIFT                   7
/* FCNFG Bit Fields */
#define FTMRE_FCNFG_ERSAREQ_MASK                 0x20u
#define FTMRE_FCNFG_ERSAREQ_SHIFT                5
#define FTMRE_FCNFG_CCIE_MASK                    0x80u
#define FTMRE_FCNFG_CCIE_SHIFT                   7
/* FCCOBLO Bit Fields */
#define FTMRE_FCCOBLO_CCOB_MASK                  0xFFu
#define FTMRE_FCCOBLO_CCOB_SHIFT                 0
#define FTMRE_FCCOBLO_CCOB(x)                    (((uint8_t)(((uint8_t)(x))<<FTMRE_FCCOBLO_CCOB_SHIFT))&FTMRE_FCCOBLO_CCOB_MASK)
/* FCCOBHI Bit Fields */
#define FTMRE_FCCOBHI_CCOB_MASK                  0xFFu
#define FTMRE_FCCOBHI_CCOB_SHIFT                 0
#define FTMRE_FCCOBHI_CCOB(x)                    (((uint8_t)(((uint8_t)(x))<<FTMRE_FCCOBHI_CCOB_SHIFT))&FTMRE_FCCOBHI_CCOB_MASK)
/* FPROT Bit Fields */
#define FTMRE_FPROT_FPLS_MASK                    0x3u
#define FTMRE_FPROT_FPLS_SHIFT                   0
#define FTMRE_FPROT_FPLS(x)                      (((uint8_t)(((uint8_t)(x))<<FTMRE_FPROT_FPLS_SHIFT))&FTMRE_FPROT_FPLS_MASK)
#define FTMRE_FPROT_FPLDIS_MASK                  0x4u
#define FTMRE_FPROT_FPLDIS_SHIFT                 2
#define FTMRE_FPROT_FPHS_MASK                    0x18u
#define FTMRE_FPROT_FPHS_SHIFT                   3
#define FTMRE_FPROT_FPHS(x)                      (((uint8_t)(((uint8_t)(x))<<FTMRE_FPROT_FPHS_SHIFT))&FTMRE_FPROT_FPHS_MASK)
#define FTMRE_FPROT_FPHDIS_MASK                  0x20u
#define FTMRE_FPROT_FPHDIS_SHIFT                 5
#define FTMRE_FPROT_RNV6_MASK                    0x40u
#define FTMRE_FPROT_RNV6_SHIFT                   6
#define FTMRE_FPROT_FPOPEN_MASK                  0x80u
#define FTMRE_FPROT_FPOPEN_SHIFT                 7
/* FOPT Bit Fields */
#define FTMRE_FOPT_NV_MASK                       0xFFu
#define FTMRE_FOPT_NV_SHIFT                      0
#define FTMRE_FOPT_NV(x)                         (((uint8_t)(((uint8_t)(x))<<FTMRE_FOPT_NV_SHIFT))&FTMRE_FOPT_NV_MASK)

/*!
 * @}
 */ /* end of group FTMRE_Register_Masks */


/* FTMRE - Peripheral instance base addresses */
/** Peripheral FTMRE base address */
#define FTMRE_BASE                               (0x40020000u)
/** Peripheral FTMRE base pointer */
#define FTMRE                                    ((FTMRE_Type *)FTMRE_BASE)
#define FTMRE_BASE_PTR                           (FTMRE)
/** Array initializer of FTMRE peripheral base addresses */
#define FTMRE_BASE_ADDRS                         { FTMRE_BASE }
/** Array initializer of FTMRE peripheral base pointers */
#define FTMRE_BASE_PTRS                          { FTMRE }

/* ----------------------------------------------------------------------------
   -- FTMRE - Register accessor macros
   ---------------------------------------------------------------------------- */

/*!
 * @addtogroup FTMRE_Register_Accessor_Macros FTMRE - Register accessor macros
 * @{
 */


/* FTMRE - Register instance definitions */
/* FTMRE */
#define FTMRE_FCCOBIX                            FTMRE_FCCOBIX_REG(FTMRE)
#define FTMRE_FSEC                               FTMRE_FSEC_REG(FTMRE)
#define FTMRE_FCLKDIV                            FTMRE_FCLKDIV_REG(FTMRE)
#define FTMRE_FSTAT                              FTMRE_FSTAT_REG(FTMRE)
#define FTMRE_FCNFG                              FTMRE_FCNFG_REG(FTMRE)
#define FTMRE_FCCOBLO                            FTMRE_FCCOBLO_REG(FTMRE)
#define FTMRE_FCCOBHI                            FTMRE_FCCOBHI_REG(FTMRE)
#define FTMRE_FPROT                              FTMRE_FPROT_REG(FTMRE)
#define FTMRE_FOPT                               FTMRE_FOPT_REG(FTMRE)

/*!
 * @}
 */ /* end of group FTMRE_Register_Accessor_Macros */


/*!
 * @}
 */ /* end of group FTMRE_Peripheral_Access_Layer */


/* ----------------------------------------------------------------------------
   -- GPIO Peripheral Access Layer
   ---------------------------------------------------------------------------- */

/*!
 * @addtogroup GPIO_Peripheral_Access_Layer GPIO Peripheral Access Layer
 * @{
 */

/** GPIO - Register Layout Typedef */
typedef struct {
  __IO uint32_t PDOR;                              /**< Port Data Output Register, offset: 0x0 */
  __O  uint32_t PSOR;                              /**< Port Set Output Register, offset: 0x4 */
  __O  uint32_t PCOR;                              /**< Port Clear Output Register, offset: 0x8 */
  __O  uint32_t PTOR;                              /**< Port Toggle Output Register, offset: 0xC */
  __I  uint32_t PDIR;                              /**< Port Data Input Register, offset: 0x10 */
  __IO uint32_t PDDR;                              /**< Port Data Direction Register, offset: 0x14 */
  __IO uint32_t PIDR;                              /**< Port Input Disable Register, offset: 0x18 */
} GPIO_Type, *GPIO_MemMapPtr;

/* ----------------------------------------------------------------------------
   -- GPIO - Register accessor macros
   ---------------------------------------------------------------------------- */

/*!
 * @addtogroup GPIO_Register_Accessor_Macros GPIO - Register accessor macros
 * @{
 */


/* GPIO - Register accessors */
#define GPIO_PDOR_REG(base)                      ((base)->PDOR)
#define GPIO_PSOR_REG(base)                      ((base)->PSOR)
#define GPIO_PCOR_REG(base)                      ((base)->PCOR)
#define GPIO_PTOR_REG(base)                      ((base)->PTOR)
#define GPIO_PDIR_REG(base)                      ((base)->PDIR)
#define GPIO_PDDR_REG(base)                      ((base)->PDDR)
#define GPIO_PIDR_REG(base)                      ((base)->PIDR)

/*!
 * @}
 */ /* end of group GPIO_Register_Accessor_Macros */


/* ----------------------------------------------------------------------------
   -- GPIO Register Masks
   ---------------------------------------------------------------------------- */

/*!
 * @addtogroup GPIO_Register_Masks GPIO Register Masks
 * @{
 */

/* PDOR Bit Fields */
#define GPIO_PDOR_PDO_MASK                       0xFFFFFFFFu
#define GPIO_PDOR_PDO_SHIFT                      0
#define GPIO_PDOR_PDO(x)                         (((uint32_t)(((uint32_t)(x))<<GPIO_PDOR_PDO_SHIFT))&GPIO_PDOR_PDO_MASK)
/* PSOR Bit Fields */
#define GPIO_PSOR_PTSO_MASK                      0xFFFFFFFFu
#define GPIO_PSOR_PTSO_SHIFT                     0
#define GPIO_PSOR_PTSO(x)                        (((uint32_t)(((uint32_t)(x))<<GPIO_PSOR_PTSO_SHIFT))&GPIO_PSOR_PTSO_MASK)
/* PCOR Bit Fields */
#define GPIO_PCOR_PTCO_MASK                      0xFFFFFFFFu
#define GPIO_PCOR_PTCO_SHIFT                     0
#define GPIO_PCOR_PTCO(x)                        (((uint32_t)(((uint32_t)(x))<<GPIO_PCOR_PTCO_SHIFT))&GPIO_PCOR_PTCO_MASK)
/* PTOR Bit Fields */
#define GPIO_PTOR_PTTO_MASK                      0xFFFFFFFFu
#define GPIO_PTOR_PTTO_SHIFT                     0
#define GPIO_PTOR_PTTO(x)                        (((uint32_t)(((uint32_t)(x))<<GPIO_PTOR_PTTO_SHIFT))&GPIO_PTOR_PTTO_MASK)
/* PDIR Bit Fields */
#define GPIO_PDIR_PDI_MASK                       0xFFFFFFFFu
#define GPIO_PDIR_PDI_SHIFT                      0
#define GPIO_PDIR_PDI(x)                         (((uint32_t)(((uint32_t)(x))<<GPIO_PDIR_PDI_SHIFT))&GPIO_PDIR_PDI_MASK)
/* PDDR Bit Fields */
#define GPIO_PDDR_PDD_MASK                       0xFFFFFFFFu
#define GPIO_PDDR_PDD_SHIFT                      0
#define GPIO_PDDR_PDD(x)                         (((uint32_t)(((uint32_t)(x))<<GPIO_PDDR_PDD_SHIFT))&GPIO_PDDR_PDD_MASK)
/* PIDR Bit Fields */
#define GPIO_PIDR_PID_MASK                       0xFFFFFFFFu
#define GPIO_PIDR_PID_SHIFT                      0
#define GPIO_PIDR_PID(x)                         (((uint32_t)(((uint32_t)(x))<<GPIO_PIDR_PID_SHIFT))&GPIO_PIDR_PID_MASK)

/*!
 * @}
 */ /* end of group GPIO_Register_Masks */


/* GPIO - Peripheral instance base addresses */
/** Peripheral GPIOA base address */
#define GPIOA_BASE                               (0x400FF000u)
/** Peripheral GPIOA base pointer */
#define GPIOA                                    ((GPIO_Type *)GPIOA_BASE)
#define GPIOA_BASE_PTR                           (GPIOA)
/** Peripheral GPIOB base address */
#define GPIOB_BASE                               (0x400FF040u)
/** Peripheral GPIOB base pointer */
#define GPIOB                                    ((GPIO_Type *)GPIOB_BASE)
#define GPIOB_BASE_PTR                           (GPIOB)
/** Peripheral GPIOC base address */
#define GPIOC_BASE                               (0x400FF080u)
/** Peripheral GPIOC base pointer */
#define GPIOC                                    ((GPIO_Type *)GPIOC_BASE)
#define GPIOC_BASE_PTR                           (GPIOC)
/** Array initializer of GPIO peripheral base addresses */
#define GPIO_BASE_ADDRS                          { GPIOA_BASE, GPIOB_BASE, GPIOC_BASE }
/** Array initializer of GPIO peripheral base pointers */
#define GPIO_BASE_PTRS                           { GPIOA, GPIOB, GPIOC }

/* ----------------------------------------------------------------------------
   -- GPIO - Register accessor macros
   ---------------------------------------------------------------------------- */

/*!
 * @addtogroup GPIO_Register_Accessor_Macros GPIO - Register accessor macros
 * @{
 */


/* GPIO - Register instance definitions */
/* GPIOA */
#define GPIOA_PDOR                               GPIO_PDOR_REG(GPIOA)
#define GPIOA_PSOR                               GPIO_PSOR_REG(GPIOA)
#define GPIOA_PCOR                               GPIO_PCOR_REG(GPIOA)
#define GPIOA_PTOR                               GPIO_PTOR_REG(GPIOA)
#define GPIOA_PDIR                               GPIO_PDIR_REG(GPIOA)
#define GPIOA_PDDR                               GPIO_PDDR_REG(GPIOA)
#define GPIOA_PIDR                               GPIO_PIDR_REG(GPIOA)
/* GPIOB */
#define GPIOB_PDOR                               GPIO_PDOR_REG(GPIOB)
#define GPIOB_PSOR                               GPIO_PSOR_REG(GPIOB)
#define GPIOB_PCOR                               GPIO_PCOR_REG(GPIOB)
#define GPIOB_PTOR                               GPIO_PTOR_REG(GPIOB)
#define GPIOB_PDIR                               GPIO_PDIR_REG(GPIOB)
#define GPIOB_PDDR                               GPIO_PDDR_REG(GPIOB)
#define GPIOB_PIDR                               GPIO_PIDR_REG(GPIOB)
/* GPIOC */
#define GPIOC_PDOR                               GPIO_PDOR_REG(GPIOC)
#define GPIOC_PSOR                               GPIO_PSOR_REG(GPIOC)
#define GPIOC_PCOR                               GPIO_PCOR_REG(GPIOC)
#define GPIOC_PTOR                               GPIO_PTOR_REG(GPIOC)
#define GPIOC_PDIR                               GPIO_PDIR_REG(GPIOC)
#define GPIOC_PDDR                               GPIO_PDDR_REG(GPIOC)
#define GPIOC_PIDR                               GPIO_PIDR_REG(GPIOC)

/*!
 * @}
 */ /* end of group GPIO_Register_Accessor_Macros */


/*!
 * @}
 */ /* end of group GPIO_Peripheral_Access_Layer */


/* ----------------------------------------------------------------------------
   -- I2C Peripheral Access Layer
   ---------------------------------------------------------------------------- */

/*!
 * @addtogroup I2C_Peripheral_Access_Layer I2C Peripheral Access Layer
 * @{
 */

/** I2C - Register Layout Typedef */
typedef struct {
  __IO uint8_t A1;                                 /**< I2C Address Register 1, offset: 0x0 */
  __IO uint8_t F;                                  /**< I2C Frequency Divider register, offset: 0x1 */
  __IO uint8_t C1;                                 /**< I2C Control Register 1, offset: 0x2 */
  __IO uint8_t S1;                                 /**< I2C Status register 1, offset: 0x3 */
  __IO uint8_t D;                                  /**< I2C Data I/O register, offset: 0x4 */
  __IO uint8_t C2;                                 /**< I2C Control Register 2, offset: 0x5 */
  __IO uint8_t FLT;                                /**< I2C Programmable Input Glitch Filter register, offset: 0x6 */
  __IO uint8_t RA;                                 /**< I2C Range Address register, offset: 0x7 */
  __IO uint8_t SMB;                                /**< I2C SMBus Control and Status register, offset: 0x8 */
  __IO uint8_t A2;                                 /**< I2C Address Register 2, offset: 0x9 */
  __IO uint8_t SLTH;                               /**< I2C SCL Low Timeout Register High, offset: 0xA */
  __IO uint8_t SLTL;                               /**< I2C SCL Low Timeout Register Low, offset: 0xB */
} I2C_Type, *I2C_MemMapPtr;

/* ----------------------------------------------------------------------------
   -- I2C - Register accessor macros
   ---------------------------------------------------------------------------- */

/*!
 * @addtogroup I2C_Register_Accessor_Macros I2C - Register accessor macros
 * @{
 */


/* I2C - Register accessors */
#define I2C_A1_REG(base)                         ((base)->A1)
#define I2C_F_REG(base)                          ((base)->F)
#define I2C_C1_REG(base)                         ((base)->C1)
#define I2C_S1_REG(base)                         ((base)->S1)
#define I2C_D_REG(base)                          ((base)->D)
#define I2C_C2_REG(base)                         ((base)->C2)
#define I2C_FLT_REG(base)                        ((base)->FLT)
#define I2C_RA_REG(base)                         ((base)->RA)
#define I2C_SMB_REG(base)                        ((base)->SMB)
#define I2C_A2_REG(base)                         ((base)->A2)
#define I2C_SLTH_REG(base)                       ((base)->SLTH)
#define I2C_SLTL_REG(base)                       ((base)->SLTL)

/*!
 * @}
 */ /* end of group I2C_Register_Accessor_Macros */


/* ----------------------------------------------------------------------------
   -- I2C Register Masks
   ---------------------------------------------------------------------------- */

/*!
 * @addtogroup I2C_Register_Masks I2C Register Masks
 * @{
 */

/* A1 Bit Fields */
#define I2C_A1_AD_MASK                           0xFEu
#define I2C_A1_AD_SHIFT                          1
#define I2C_A1_AD(x)                             (((uint8_t)(((uint8_t)(x))<<I2C_A1_AD_SHIFT))&I2C_A1_AD_MASK)
/* F Bit Fields */
#define I2C_F_ICR_MASK                           0x3Fu
#define I2C_F_ICR_SHIFT                          0
#define I2C_F_ICR(x)                             (((uint8_t)(((uint8_t)(x))<<I2C_F_ICR_SHIFT))&I2C_F_ICR_MASK)
#define I2C_F_MULT_MASK                          0xC0u
#define I2C_F_MULT_SHIFT                         6
#define I2C_F_MULT(x)                            (((uint8_t)(((uint8_t)(x))<<I2C_F_MULT_SHIFT))&I2C_F_MULT_MASK)
/* C1 Bit Fields */
#define I2C_C1_WUEN_MASK                         0x2u
#define I2C_C1_WUEN_SHIFT                        1
#define I2C_C1_RSTA_MASK                         0x4u
#define I2C_C1_RSTA_SHIFT                        2
#define I2C_C1_TXAK_MASK                         0x8u
#define I2C_C1_TXAK_SHIFT                        3
#define I2C_C1_TX_MASK                           0x10u
#define I2C_C1_TX_SHIFT                          4
#define I2C_C1_MST_MASK                          0x20u
#define I2C_C1_MST_SHIFT                         5
#define I2C_C1_IICIE_MASK                        0x40u
#define I2C_C1_IICIE_SHIFT                       6
#define I2C_C1_IICEN_MASK                        0x80u
#define I2C_C1_IICEN_SHIFT                       7
/* S1 Bit Fields */
#define I2C_S1_RXAK_MASK                         0x1u
#define I2C_S1_RXAK_SHIFT                        0
#define I2C_S1_IICIF_MASK                        0x2u
#define I2C_S1_IICIF_SHIFT                       1
#define I2C_S1_SRW_MASK                          0x4u
#define I2C_S1_SRW_SHIFT                         2
#define I2C_S1_RAM_MASK                          0x8u
#define I2C_S1_RAM_SHIFT                         3
#define I2C_S1_ARBL_MASK                         0x10u
#define I2C_S1_ARBL_SHIFT                        4
#define I2C_S1_BUSY_MASK                         0x20u
#define I2C_S1_BUSY_SHIFT                        5
#define I2C_S1_IAAS_MASK                         0x40u
#define I2C_S1_IAAS_SHIFT                        6
#define I2C_S1_TCF_MASK                          0x80u
#define I2C_S1_TCF_SHIFT                         7
/* D Bit Fields */
#define I2C_D_DATA_MASK                          0xFFu
#define I2C_D_DATA_SHIFT                         0
#define I2C_D_DATA(x)                            (((uint8_t)(((uint8_t)(x))<<I2C_D_DATA_SHIFT))&I2C_D_DATA_MASK)
/* C2 Bit Fields */
#define I2C_C2_AD_MASK                           0x7u
#define I2C_C2_AD_SHIFT                          0
#define I2C_C2_AD(x)                             (((uint8_t)(((uint8_t)(x))<<I2C_C2_AD_SHIFT))&I2C_C2_AD_MASK)
#define I2C_C2_RMEN_MASK                         0x8u
#define I2C_C2_RMEN_SHIFT                        3
#define I2C_C2_SBRC_MASK                         0x10u
#define I2C_C2_SBRC_SHIFT                        4
#define I2C_C2_ADEXT_MASK                        0x40u
#define I2C_C2_ADEXT_SHIFT                       6
#define I2C_C2_GCAEN_MASK                        0x80u
#define I2C_C2_GCAEN_SHIFT                       7
/* FLT Bit Fields */
#define I2C_FLT_FLT_MASK                         0xFu
#define I2C_FLT_FLT_SHIFT                        0
#define I2C_FLT_FLT(x)                           (((uint8_t)(((uint8_t)(x))<<I2C_FLT_FLT_SHIFT))&I2C_FLT_FLT_MASK)
#define I2C_FLT_STARTF_MASK                      0x10u
#define I2C_FLT_STARTF_SHIFT                     4
#define I2C_FLT_SSIE_MASK                        0x20u
#define I2C_FLT_SSIE_SHIFT                       5
#define I2C_FLT_STOPF_MASK                       0x40u
#define I2C_FLT_STOPF_SHIFT                      6
#define I2C_FLT_SHEN_MASK                        0x80u
#define I2C_FLT_SHEN_SHIFT                       7
/* RA Bit Fields */
#define I2C_RA_RAD_MASK                          0xFEu
#define I2C_RA_RAD_SHIFT                         1
#define I2C_RA_RAD(x)                            (((uint8_t)(((uint8_t)(x))<<I2C_RA_RAD_SHIFT))&I2C_RA_RAD_MASK)
/* SMB Bit Fields */
#define I2C_SMB_SHTF2IE_MASK                     0x1u
#define I2C_SMB_SHTF2IE_SHIFT                    0
#define I2C_SMB_SHTF2_MASK                       0x2u
#define I2C_SMB_SHTF2_SHIFT                      1
#define I2C_SMB_SHTF1_MASK                       0x4u
#define I2C_SMB_SHTF1_SHIFT                      2
#define I2C_SMB_SLTF_MASK                        0x8u
#define I2C_SMB_SLTF_SHIFT                       3
#define I2C_SMB_TCKSEL_MASK                      0x10u
#define I2C_SMB_TCKSEL_SHIFT                     4
#define I2C_SMB_SIICAEN_MASK                     0x20u
#define I2C_SMB_SIICAEN_SHIFT                    5
#define I2C_SMB_ALERTEN_MASK                     0x40u
#define I2C_SMB_ALERTEN_SHIFT                    6
#define I2C_SMB_FACK_MASK                        0x80u
#define I2C_SMB_FACK_SHIFT                       7
/* A2 Bit Fields */
#define I2C_A2_SAD_MASK                          0xFEu
#define I2C_A2_SAD_SHIFT                         1
#define I2C_A2_SAD(x)                            (((uint8_t)(((uint8_t)(x))<<I2C_A2_SAD_SHIFT))&I2C_A2_SAD_MASK)
/* SLTH Bit Fields */
#define I2C_SLTH_SSLT_MASK                       0xFFu
#define I2C_SLTH_SSLT_SHIFT                      0
#define I2C_SLTH_SSLT(x)                         (((uint8_t)(((uint8_t)(x))<<I2C_SLTH_SSLT_SHIFT))&I2C_SLTH_SSLT_MASK)
/* SLTL Bit Fields */
#define I2C_SLTL_SSLT_MASK                       0xFFu
#define I2C_SLTL_SSLT_SHIFT                      0
#define I2C_SLTL_SSLT(x)                         (((uint8_t)(((uint8_t)(x))<<I2C_SLTL_SSLT_SHIFT))&I2C_SLTL_SSLT_MASK)

/*!
 * @}
 */ /* end of group I2C_Register_Masks */


/* I2C - Peripheral instance base addresses */
/** Peripheral I2C0 base address */
#define I2C0_BASE                                (0x40066000u)
/** Peripheral I2C0 base pointer */
#define I2C0                                     ((I2C_Type *)I2C0_BASE)
#define I2C0_BASE_PTR                            (I2C0)
/** Peripheral I2C1 base address */
#define I2C1_BASE                                (0x40067000u)
/** Peripheral I2C1 base pointer */
#define I2C1                                     ((I2C_Type *)I2C1_BASE)
#define I2C1_BASE_PTR                            (I2C1)
/** Array initializer of I2C peripheral base addresses */
#define I2C_BASE_ADDRS                           { I2C0_BASE, I2C1_BASE }
/** Array initializer of I2C peripheral base pointers */
#define I2C_BASE_PTRS                            { I2C0, I2C1 }

/* ----------------------------------------------------------------------------
   -- I2C - Register accessor macros
   ---------------------------------------------------------------------------- */

/*!
 * @addtogroup I2C_Register_Accessor_Macros I2C - Register accessor macros
 * @{
 */


/* I2C - Register instance definitions */
/* I2C0 */
#define I2C0_A1                                  I2C_A1_REG(I2C0)
#define I2C0_F                                   I2C_F_REG(I2C0)
#define I2C0_C1                                  I2C_C1_REG(I2C0)
#define I2C0_S1                                  I2C_S1_REG(I2C0)
#define I2C0_D                                   I2C_D_REG(I2C0)
#define I2C0_C2                                  I2C_C2_REG(I2C0)
#define I2C0_FLT                                 I2C_FLT_REG(I2C0)
#define I2C0_RA                                  I2C_RA_REG(I2C0)
#define I2C0_SMB                                 I2C_SMB_REG(I2C0)
#define I2C0_A2                                  I2C_A2_REG(I2C0)
#define I2C0_SLTH                                I2C_SLTH_REG(I2C0)
#define I2C0_SLTL                                I2C_SLTL_REG(I2C0)
/* I2C1 */
#define I2C1_A1                                  I2C_A1_REG(I2C1)
#define I2C1_F                                   I2C_F_REG(I2C1)
#define I2C1_C1                                  I2C_C1_REG(I2C1)
#define I2C1_S1                                  I2C_S1_REG(I2C1)
#define I2C1_D                                   I2C_D_REG(I2C1)
#define I2C1_C2                                  I2C_C2_REG(I2C1)
#define I2C1_FLT                                 I2C_FLT_REG(I2C1)
#define I2C1_RA                                  I2C_RA_REG(I2C1)
#define I2C1_SMB                                 I2C_SMB_REG(I2C1)
#define I2C1_A2                                  I2C_A2_REG(I2C1)
#define I2C1_SLTH                                I2C_SLTH_REG(I2C1)
#define I2C1_SLTL                                I2C_SLTL_REG(I2C1)

/*!
 * @}
 */ /* end of group I2C_Register_Accessor_Macros */


/*!
 * @}
 */ /* end of group I2C_Peripheral_Access_Layer */


/* ----------------------------------------------------------------------------
   -- ICS Peripheral Access Layer
   ---------------------------------------------------------------------------- */

/*!
 * @addtogroup ICS_Peripheral_Access_Layer ICS Peripheral Access Layer
 * @{
 */

/** ICS - Register Layout Typedef */
typedef struct {
  __IO uint8_t C1;                                 /**< ICS Control Register 1, offset: 0x0 */
  __IO uint8_t C2;                                 /**< ICS Control Register 2, offset: 0x1 */
  __IO uint8_t C3;                                 /**< ICS Control Register 3, offset: 0x2 */
  __IO uint8_t C4;                                 /**< ICS Control Register 4, offset: 0x3 */
  __IO uint8_t S;                                  /**< ICS Status Register, offset: 0x4 */
} ICS_Type, *ICS_MemMapPtr;

/* ----------------------------------------------------------------------------
   -- ICS - Register accessor macros
   ---------------------------------------------------------------------------- */

/*!
 * @addtogroup ICS_Register_Accessor_Macros ICS - Register accessor macros
 * @{
 */


/* ICS - Register accessors */
#define ICS_C1_REG(base)                         ((base)->C1)
#define ICS_C2_REG(base)                         ((base)->C2)
#define ICS_C3_REG(base)                         ((base)->C3)
#define ICS_C4_REG(base)                         ((base)->C4)
#define ICS_S_REG(base)                          ((base)->S)

/*!
 * @}
 */ /* end of group ICS_Register_Accessor_Macros */


/* ----------------------------------------------------------------------------
   -- ICS Register Masks
   ---------------------------------------------------------------------------- */

/*!
 * @addtogroup ICS_Register_Masks ICS Register Masks
 * @{
 */

/* C1 Bit Fields */
#define ICS_C1_IREFSTEN_MASK                     0x1u
#define ICS_C1_IREFSTEN_SHIFT                    0
#define ICS_C1_IRCLKEN_MASK                      0x2u
#define ICS_C1_IRCLKEN_SHIFT                     1
#define ICS_C1_IREFS_MASK                        0x4u
#define ICS_C1_IREFS_SHIFT                       2
#define ICS_C1_RDIV_MASK                         0x38u
#define ICS_C1_RDIV_SHIFT                        3
#define ICS_C1_RDIV(x)                           (((uint8_t)(((uint8_t)(x))<<ICS_C1_RDIV_SHIFT))&ICS_C1_RDIV_MASK)
#define ICS_C1_CLKS_MASK                         0xC0u
#define ICS_C1_CLKS_SHIFT                        6
#define ICS_C1_CLKS(x)                           (((uint8_t)(((uint8_t)(x))<<ICS_C1_CLKS_SHIFT))&ICS_C1_CLKS_MASK)
/* C2 Bit Fields */
#define ICS_C2_LP_MASK                           0x10u
#define ICS_C2_LP_SHIFT                          4
#define ICS_C2_BDIV_MASK                         0xE0u
#define ICS_C2_BDIV_SHIFT                        5
#define ICS_C2_BDIV(x)                           (((uint8_t)(((uint8_t)(x))<<ICS_C2_BDIV_SHIFT))&ICS_C2_BDIV_MASK)
/* C3 Bit Fields */
#define ICS_C3_SCTRIM_MASK                       0xFFu
#define ICS_C3_SCTRIM_SHIFT                      0
#define ICS_C3_SCTRIM(x)                         (((uint8_t)(((uint8_t)(x))<<ICS_C3_SCTRIM_SHIFT))&ICS_C3_SCTRIM_MASK)
/* C4 Bit Fields */
#define ICS_C4_SCFTRIM_MASK                      0x1u
#define ICS_C4_SCFTRIM_SHIFT                     0
#define ICS_C4_CME_MASK                          0x20u
#define ICS_C4_CME_SHIFT                         5
#define ICS_C4_LOLIE_MASK                        0x80u
#define ICS_C4_LOLIE_SHIFT                       7
/* S Bit Fields */
#define ICS_S_CLKST_MASK                         0xCu
#define ICS_S_CLKST_SHIFT                        2
#define ICS_S_CLKST(x)                           (((uint8_t)(((uint8_t)(x))<<ICS_S_CLKST_SHIFT))&ICS_S_CLKST_MASK)
#define ICS_S_IREFST_MASK                        0x10u
#define ICS_S_IREFST_SHIFT                       4
#define ICS_S_LOCK_MASK                          0x40u
#define ICS_S_LOCK_SHIFT                         6
#define ICS_S_LOLS_MASK                          0x80u
#define ICS_S_LOLS_SHIFT                         7

/*!
 * @}
 */ /* end of group ICS_Register_Masks */


/* ICS - Peripheral instance base addresses */
/** Peripheral ICS base address */
#define ICS_BASE                                 (0x40064000u)
/** Peripheral ICS base pointer */
#define ICS                                      ((ICS_Type *)ICS_BASE)
#define ICS_BASE_PTR                             (ICS)
/** Array initializer of ICS peripheral base addresses */
#define ICS_BASE_ADDRS                           { ICS_BASE }
/** Array initializer of ICS peripheral base pointers */
#define ICS_BASE_PTRS                            { ICS }

/* ----------------------------------------------------------------------------
   -- ICS - Register accessor macros
   ---------------------------------------------------------------------------- */

/*!
 * @addtogroup ICS_Register_Accessor_Macros ICS - Register accessor macros
 * @{
 */


/* ICS - Register instance definitions */
/* ICS */
#define ICS_C1                                   ICS_C1_REG(ICS)
#define ICS_C2                                   ICS_C2_REG(ICS)
#define ICS_C3                                   ICS_C3_REG(ICS)
#define ICS_C4                                   ICS_C4_REG(ICS)
#define ICS_S                                    ICS_S_REG(ICS)

/*!
 * @}
 */ /* end of group ICS_Register_Accessor_Macros */


/*!
 * @}
 */ /* end of group ICS_Peripheral_Access_Layer */


/* ----------------------------------------------------------------------------
   -- IRQ Peripheral Access Layer
   ---------------------------------------------------------------------------- */

/*!
 * @addtogroup IRQ_Peripheral_Access_Layer IRQ Peripheral Access Layer
 * @{
 */

/** IRQ - Register Layout Typedef */
typedef struct {
  __IO uint8_t SC;                                 /**< Interrupt Pin Request Status and Control Register, offset: 0x0 */
} IRQ_Type, *IRQ_MemMapPtr;

/* ----------------------------------------------------------------------------
   -- IRQ - Register accessor macros
   ---------------------------------------------------------------------------- */

/*!
 * @addtogroup IRQ_Register_Accessor_Macros IRQ - Register accessor macros
 * @{
 */


/* IRQ - Register accessors */
#define IRQ_SC_REG(base)                         ((base)->SC)

/*!
 * @}
 */ /* end of group IRQ_Register_Accessor_Macros */


/* ----------------------------------------------------------------------------
   -- IRQ Register Masks
   ---------------------------------------------------------------------------- */

/*!
 * @addtogroup IRQ_Register_Masks IRQ Register Masks
 * @{
 */

/* SC Bit Fields */
#define IRQ_SC_IRQMOD_MASK                       0x1u
#define IRQ_SC_IRQMOD_SHIFT                      0
#define IRQ_SC_IRQIE_MASK                        0x2u
#define IRQ_SC_IRQIE_SHIFT                       1
#define IRQ_SC_IRQACK_MASK                       0x4u
#define IRQ_SC_IRQACK_SHIFT                      2
#define IRQ_SC_IRQF_MASK                         0x8u
#define IRQ_SC_IRQF_SHIFT                        3
#define IRQ_SC_IRQPE_MASK                        0x10u
#define IRQ_SC_IRQPE_SHIFT                       4
#define IRQ_SC_IRQEDG_MASK                       0x20u
#define IRQ_SC_IRQEDG_SHIFT                      5
#define IRQ_SC_IRQPDD_MASK                       0x40u
#define IRQ_SC_IRQPDD_SHIFT                      6

/*!
 * @}
 */ /* end of group IRQ_Register_Masks */


/* IRQ - Peripheral instance base addresses */
/** Peripheral IRQ base address */
#define IRQ_BASE                                 (0x40031000u)
/** Peripheral IRQ base pointer */
#define IRQ                                      ((IRQ_Type *)IRQ_BASE)
#define IRQ_BASE_PTR                             (IRQ)
/** Array initializer of IRQ peripheral base addresses */
#define IRQ_BASE_ADDRS                           { IRQ_BASE }
/** Array initializer of IRQ peripheral base pointers */
#define IRQ_BASE_PTRS                            { IRQ }

/* ----------------------------------------------------------------------------
   -- IRQ - Register accessor macros
   ---------------------------------------------------------------------------- */

/*!
 * @addtogroup IRQ_Register_Accessor_Macros IRQ - Register accessor macros
 * @{
 */


/* IRQ - Register instance definitions */
/* IRQ */
#define IRQ_SC                                   IRQ_SC_REG(IRQ)

/*!
 * @}
 */ /* end of group IRQ_Register_Accessor_Macros */


/*!
 * @}
 */ /* end of group IRQ_Peripheral_Access_Layer */


/* ----------------------------------------------------------------------------
   -- KBI Peripheral Access Layer
   ---------------------------------------------------------------------------- */

/*!
 * @addtogroup KBI_Peripheral_Access_Layer KBI Peripheral Access Layer
 * @{
 */

/** KBI - Register Layout Typedef */
typedef struct {
  __IO uint32_t PE;                                /**< KBI Pin Enable Register, offset: 0x0 */
  __IO uint32_t ES;                                /**< KBI Edge Select Register, offset: 0x4 */
  __IO uint32_t SC;                                /**< KBI Status and Control Register, offset: 0x8 */
  __I  uint32_t SP;                                /**< KBI Source Pin Register, offset: 0xC */
} KBI_Type, *KBI_MemMapPtr;

/* ----------------------------------------------------------------------------
   -- KBI - Register accessor macros
   ---------------------------------------------------------------------------- */

/*!
 * @addtogroup KBI_Register_Accessor_Macros KBI - Register accessor macros
 * @{
 */


/* KBI - Register accessors */
#define KBI_PE_REG(base)                         ((base)->PE)
#define KBI_ES_REG(base)                         ((base)->ES)
#define KBI_SC_REG(base)                         ((base)->SC)
#define KBI_SP_REG(base)                         ((base)->SP)

/*!
 * @}
 */ /* end of group KBI_Register_Accessor_Macros */


/* ----------------------------------------------------------------------------
   -- KBI Register Masks
   ---------------------------------------------------------------------------- */

/*!
 * @addtogroup KBI_Register_Masks KBI Register Masks
 * @{
 */

/* PE Bit Fields */
#define KBI_PE_KBIPE_MASK                        0xFFFFFFFFu
#define KBI_PE_KBIPE_SHIFT                       0
#define KBI_PE_KBIPE(x)                          (((uint32_t)(((uint32_t)(x))<<KBI_PE_KBIPE_SHIFT))&KBI_PE_KBIPE_MASK)
/* ES Bit Fields */
#define KBI_ES_KBEDG_MASK                        0xFFFFFFFFu
#define KBI_ES_KBEDG_SHIFT                       0
#define KBI_ES_KBEDG(x)                          (((uint32_t)(((uint32_t)(x))<<KBI_ES_KBEDG_SHIFT))&KBI_ES_KBEDG_MASK)
/* SC Bit Fields */
#define KBI_SC_KBMOD_MASK                        0x1u
#define KBI_SC_KBMOD_SHIFT                       0
#define KBI_SC_KBIE_MASK                         0x2u
#define KBI_SC_KBIE_SHIFT                        1
#define KBI_SC_KBACK_MASK                        0x4u
#define KBI_SC_KBACK_SHIFT                       2
#define KBI_SC_KBF_MASK                          0x8u
#define KBI_SC_KBF_SHIFT                         3
#define KBI_SC_KBSPEN_MASK                       0x10u
#define KBI_SC_KBSPEN_SHIFT                      4
#define KBI_SC_RSTKBSP_MASK                      0x20u
#define KBI_SC_RSTKBSP_SHIFT                     5
/* SP Bit Fields */
#define KBI_SP_SP_MASK                           0xFFFFFFFFu
#define KBI_SP_SP_SHIFT                          0
#define KBI_SP_SP(x)                             (((uint32_t)(((uint32_t)(x))<<KBI_SP_SP_SHIFT))&KBI_SP_SP_MASK)

/*!
 * @}
 */ /* end of group KBI_Register_Masks */


/* KBI - Peripheral instance base addresses */
/** Peripheral KBI0 base address */
#define KBI0_BASE                                (0x40079000u)
/** Peripheral KBI0 base pointer */
#define KBI0                                     ((KBI_Type *)KBI0_BASE)
#define KBI0_BASE_PTR                            (KBI0)
/** Peripheral KBI1 base address */
#define KBI1_BASE                                (0x4007A000u)
/** Peripheral KBI1 base pointer */
#define KBI1                                     ((KBI_Type *)KBI1_BASE)
#define KBI1_BASE_PTR                            (KBI1)
/** Array initializer of KBI peripheral base addresses */
#define KBI_BASE_ADDRS                           { KBI0_BASE, KBI1_BASE }
/** Array initializer of KBI peripheral base pointers */
#define KBI_BASE_PTRS                            { KBI0, KBI1 }

/* ----------------------------------------------------------------------------
   -- KBI - Register accessor macros
   ---------------------------------------------------------------------------- */

/*!
 * @addtogroup KBI_Register_Accessor_Macros KBI - Register accessor macros
 * @{
 */


/* KBI - Register instance definitions */
/* KBI0 */
#define KBI0_PE                                  KBI_PE_REG(KBI0)
#define KBI0_ES                                  KBI_ES_REG(KBI0)
#define KBI0_SC                                  KBI_SC_REG(KBI0)
#define KBI0_SP                                  KBI_SP_REG(KBI0)
/* KBI1 */
#define KBI1_PE                                  KBI_PE_REG(KBI1)
#define KBI1_ES                                  KBI_ES_REG(KBI1)
#define KBI1_SC                                  KBI_SC_REG(KBI1)
#define KBI1_SP                                  KBI_SP_REG(KBI1)

/*!
 * @}
 */ /* end of group KBI_Register_Accessor_Macros */


/*!
 * @}
 */ /* end of group KBI_Peripheral_Access_Layer */


/* ----------------------------------------------------------------------------
   -- MCM Peripheral Access Layer
   ---------------------------------------------------------------------------- */

/*!
 * @addtogroup MCM_Peripheral_Access_Layer MCM Peripheral Access Layer
 * @{
 */

/** MCM - Register Layout Typedef */
typedef struct {
       uint8_t RESERVED_0[8];
  __I  uint16_t PLASC;                             /**< Crossbar Switch (AXBS) Slave Configuration, offset: 0x8 */
  __I  uint16_t PLAMC;                             /**< Crossbar Switch (AXBS) Master Configuration, offset: 0xA */
  __IO uint32_t PLACR;                             /**< Platform Control Register, offset: 0xC */
} MCM_Type, *MCM_MemMapPtr;

/* ----------------------------------------------------------------------------
   -- MCM - Register accessor macros
   ---------------------------------------------------------------------------- */

/*!
 * @addtogroup MCM_Register_Accessor_Macros MCM - Register accessor macros
 * @{
 */


/* MCM - Register accessors */
#define MCM_PLASC_REG(base)                      ((base)->PLASC)
#define MCM_PLAMC_REG(base)                      ((base)->PLAMC)
#define MCM_PLACR_REG(base)                      ((base)->PLACR)

/*!
 * @}
 */ /* end of group MCM_Register_Accessor_Macros */


/* ----------------------------------------------------------------------------
   -- MCM Register Masks
   ---------------------------------------------------------------------------- */

/*!
 * @addtogroup MCM_Register_Masks MCM Register Masks
 * @{
 */

/* PLASC Bit Fields */
#define MCM_PLASC_ASC_MASK                       0xFFu
#define MCM_PLASC_ASC_SHIFT                      0
#define MCM_PLASC_ASC(x)                         (((uint16_t)(((uint16_t)(x))<<MCM_PLASC_ASC_SHIFT))&MCM_PLASC_ASC_MASK)
/* PLAMC Bit Fields */
#define MCM_PLAMC_AMC_MASK                       0xFFu
#define MCM_PLAMC_AMC_SHIFT                      0
#define MCM_PLAMC_AMC(x)                         (((uint16_t)(((uint16_t)(x))<<MCM_PLAMC_AMC_SHIFT))&MCM_PLAMC_AMC_MASK)
/* PLACR Bit Fields */
#define MCM_PLACR_CFCC_MASK                      0x400u
#define MCM_PLACR_CFCC_SHIFT                     10
#define MCM_PLACR_DFCDA_MASK                     0x800u
#define MCM_PLACR_DFCDA_SHIFT                    11
#define MCM_PLACR_DFCIC_MASK                     0x1000u
#define MCM_PLACR_DFCIC_SHIFT                    12
#define MCM_PLACR_DFCC_MASK                      0x2000u
#define MCM_PLACR_DFCC_SHIFT                     13
#define MCM_PLACR_EFDS_MASK                      0x4000u
#define MCM_PLACR_EFDS_SHIFT                     14
#define MCM_PLACR_DFCS_MASK                      0x8000u
#define MCM_PLACR_DFCS_SHIFT                     15
#define MCM_PLACR_ESFC_MASK                      0x10000u
#define MCM_PLACR_ESFC_SHIFT                     16

/*!
 * @}
 */ /* end of group MCM_Register_Masks */


/* MCM - Peripheral instance base addresses */
/** Peripheral MCM base address */
#define MCM_BASE                                 (0xF0003000u)
/** Peripheral MCM base pointer */
#define MCM                                      ((MCM_Type *)MCM_BASE)
#define MCM_BASE_PTR                             (MCM)
/** Array initializer of MCM peripheral base addresses */
#define MCM_BASE_ADDRS                           { MCM_BASE }
/** Array initializer of MCM peripheral base pointers */
#define MCM_BASE_PTRS                            { MCM }

/* ----------------------------------------------------------------------------
   -- MCM - Register accessor macros
   ---------------------------------------------------------------------------- */

/*!
 * @addtogroup MCM_Register_Accessor_Macros MCM - Register accessor macros
 * @{
 */


/* MCM - Register instance definitions */
/* MCM */
#define MCM_PLASC                                MCM_PLASC_REG(MCM)
#define MCM_PLAMC                                MCM_PLAMC_REG(MCM)
#define MCM_PLACR                                MCM_PLACR_REG(MCM)

/*!
 * @}
 */ /* end of group MCM_Register_Accessor_Macros */


/*!
 * @}
 */ /* end of group MCM_Peripheral_Access_Layer */


/* ----------------------------------------------------------------------------
   -- MSCAN Peripheral Access Layer
   ---------------------------------------------------------------------------- */

/*!
 * @addtogroup MSCAN_Peripheral_Access_Layer MSCAN Peripheral Access Layer
 * @{
 */
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
